MadsRudolph/vinyl-adc/docs/HANDOFF-sim.md

# Handoff — KiCad SPICE testbenches for the vinyl ADC

Paste the block below into a fresh Claude Code session started in
`C:\Users\Mads2\Documents\Projects`.

---

Build the KiCad SPICE testbenches for the discrete delta-sigma vinyl ADC.

**Use the `kicad-schematic` skill**, specifically its fifth gate and
`references/spice-testbenches.md`. `scripts/simfields.py` and
`assets/spice/behavioural.lib` in that skill are the tools; the Class D
amplifier at `Projects/Class D Amplifier/hardware/kicad/sim/` is a complete
worked example of the same job — read `tools/sim_layout.py`, `tools/run_sims.py`
and `README.md` there before starting.

## The project

`Projects/Vinyl ADC/`. The schematic phase is **finished and verified** — do not
redraw it:

- `hardware/kicad/vinyl_adc.kicad_sch`, 121 parts, A2, four bands (power,
  clock/digital, channel L, channel R), generated by
  `hardware/kicad/tools/vinyl_adc_layout.py`
- gates all passing: `sch_score.py` PASS 13/13, ERC clean apart from benign
  `lib_symbol_mismatch`, `tools/check_intent.py` PASS, PDF read twice
- `docs/design-notes.md` is the decision record and the source of every number
  the benches must assert; `docs/bom.md` is the BOM

**Two things about where files go.** There is already a `sim/` directory at the
project root holding the *Python* design tools (`modulator.py`, `components.py`,
`verify.py`, `design_search.py`). That is not this work and must not be touched
or overwritten. Put the KiCad benches in **`hardware/kicad/sim/`**, mirroring the
Class D layout. Also note the project moved into the `Documents\Projects` git
repo and is still untracked there — the stored memory says it lives at
`C:\Users\Mads2\vinyl-adc-project`, which no longer exists; fix that memory.

## What SPICE is for here, and what it is not

The Python model already predicts **68 dB SNR at −8 dBFS** and does it properly,
with long runs and an FFT. **Do not try to reproduce that number in SPICE.**
Reaching 68 dB over a 20 kHz band at 1.536 MHz and OSR 32 needs on the order of
a second of transient at nanosecond steps; it would run for hours and tell you
what `sim/verify.py` already knows.

SPICE's job is the analog reality the Python model idealises:

- op-amp GBW and slew against the TL074's real limits
- the LM311's 200 ns delay and its single-supply threshold
- the charge pump's droop under real load
- where the op-amps actually saturate — which is load-bearing (see below)

Say so on the sheets, so nobody later reads a missing SNR figure as a gap.

## Benches to build

One per block plus a whole-loop sheet, each its own KiCad project. Suggested,
but derive the final list from the schematic's own blocks:

| bench | asserts |
|---|---|
| rails + charge pump | −5 V pump from the 74HC244 with all eight outputs paralleled reaches **≈ −4.1 V at ~32 mA**, ripple **< 1 µV** after 4.7 Ω + 220 µF; pump clocked at **192 kHz** from 4040 Q5 |
| reference | `VREF_P` sits at **2.5 V**; the −2.5 V reference tracks the rail (that is deliberate — it turns rail noise into −98 dB gain modulation instead of additive noise) |
| clock divider | 1.536 MHz in, **4040 Q5 = 192 kHz**, correct division and duty |
| one integrator | gain matches its design coefficient with a real TL074, `a = [0.250, 0.320, 0.610]` normalised to fs |
| quantiser | LM311 on **single +5 V/GND**, summing node biased to +2.5 V, ~200 ns propagation |
| DAC + ELD | 74HC04 swinging 0/5 V into `R_d` with an equal resistor to −2.5 V gives net **±2.5 V**; ELD compensation `k0 = −0.225` |
| **whole loop, one channel** | the payoff sheet — see below |

## The whole-loop bench is the one that matters

Three things to check, in order of importance:

1. **The click test.** A 40 µs transient at 3× full scale, then a normal signal.
   The loop **must recover**. A 1-bit third-order loop that overloads never comes
   back on its own, and on vinyl that is not a corner case. This is the single
   most valuable thing SPICE can tell you here that the schematic cannot.
2. **Where the TL074 actually saturates.** The design has **no clamp parts** — the
   integrator state scales are chosen so the op-amps' own output saturation *is*
   the clamp, at roughly ±2.7 V on ±5 V rails, i.e. 1.3–1.8× Vref. If real
   saturation lands outside that window the rescue mechanism does not work.
   **The rail voltages and the resistor scaling are load-bearing, not arbitrary.**
3. **Integrator swings at −8 dBFS**: 1.43 / 1.47 / 1.45 V. Full scale is
   3.49 Vpk (2.47 Vrms) with the level trimmer at maximum, set by `Rin = 20k5`
   against `Rd1 = 14k7`.

Assert against **those numbers from `design-notes.md`, not against whatever your
models happen to do.** A model and a test that share the same wrong assumption
agree with each other and are both wrong — that has already happened once on the
Class D board, where an inverted comparator model passed its own test.

## Constraints

- **KiCad 10** binaries explicitly: `C:\Program Files\KiCad\10.0\bin\`
- `py -3.13` has `sexpdata`; `C:\Users\Mads2\miniconda3\python.exe` has PySpice
- **Never** run `kicad-cli sch upgrade`
- **Close KiCad before writing any file** it has open
- Every generated `.kicad_pro` needs `wire_width` in its netclasses or the sheet
  renders as invisible hairlines while ERC stays clean
- **No mention of Claude, AI or co-authorship** anywhere in commits or docs

## Done means

- every bench: ERC **0 violations**, `sch_score.py` PASS
- a `run_sims.py` harness that exports each sheet through `kicad-cli` and asserts
  the numbers above, all passing
- the board sheet carries a clickable index of the benches and each bench links
  back (`file:sim/<name>.kicad_sch` — a scheme is required, and point at the
  `.kicad_sch`, not the `.kicad_pro`)
- `design-notes.md` gains a section on what the simulations found, including
  anything that disagrees with the Python model
- committed, and the project's memory updated with the new path
