MadsRudolph/vinyl-adc/media/laser_engraved_lid.png

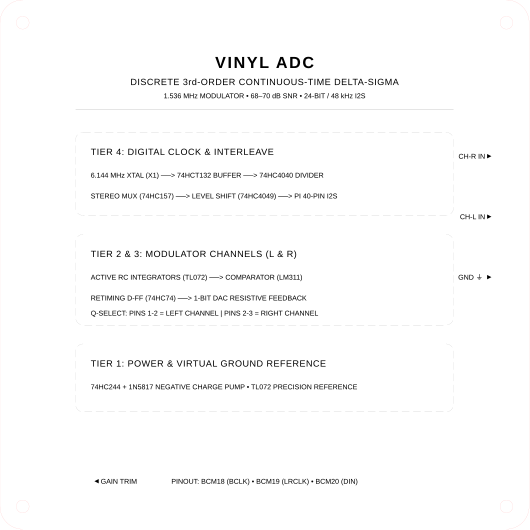
media/laser_engraved_lid.png
