MadsRudolph/vinyl-adc/media/pcb_renders/pcb_channel_top.png

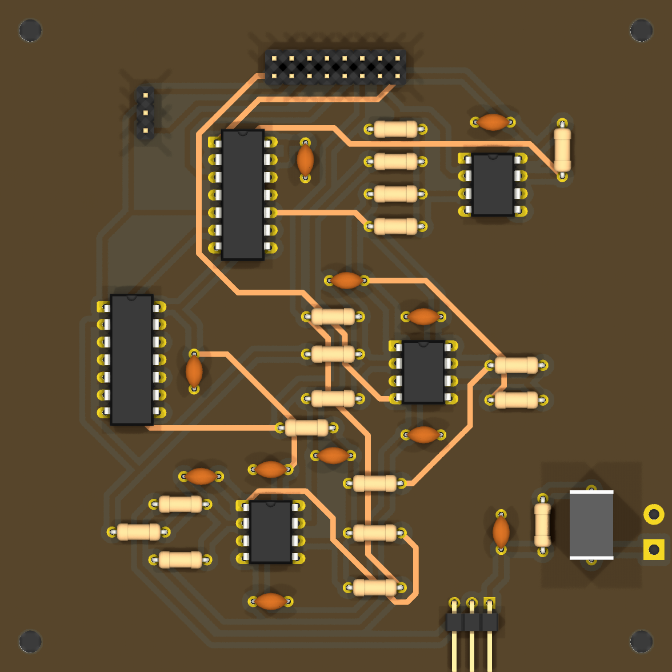
media/pcb_renders/pcb_channel_top.png
