MadsRudolph/vinyl-adc/media/pcb_renders/pcb_digital_top.png

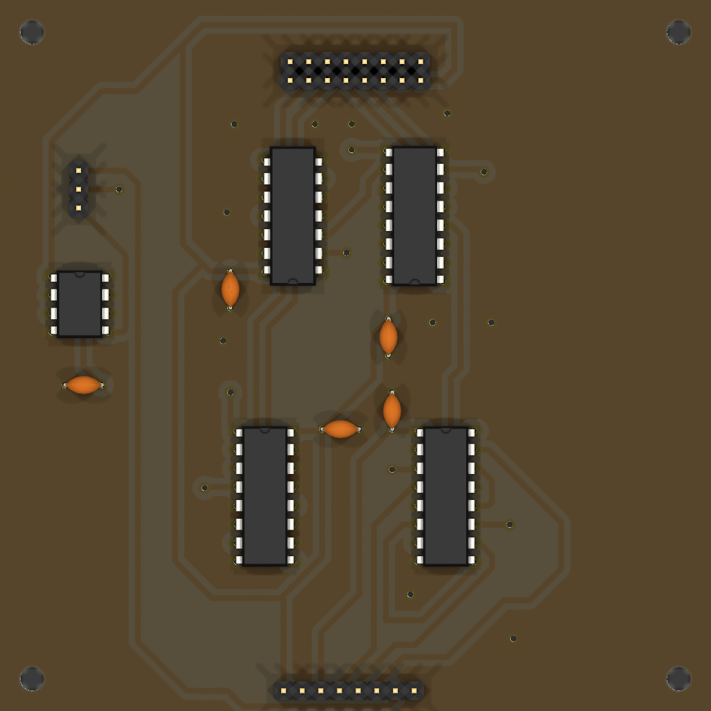
media/pcb_renders/pcb_digital_top.png
