MadsRudolph/vinyl-adc/media/pcb_renders/pcb_power_top.png

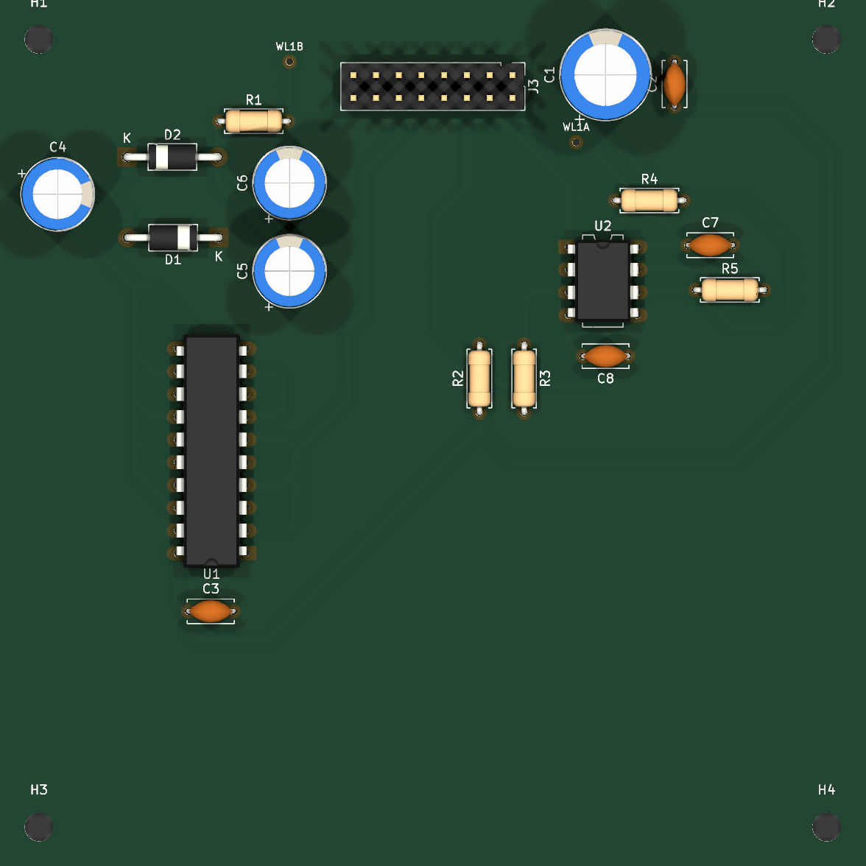
media/pcb_renders/pcb_power_top.png
