MadsRudolph/vinyl-adc/production/vinyl_adc_rev_e/vinyl_adc_rev_e-bottom.png

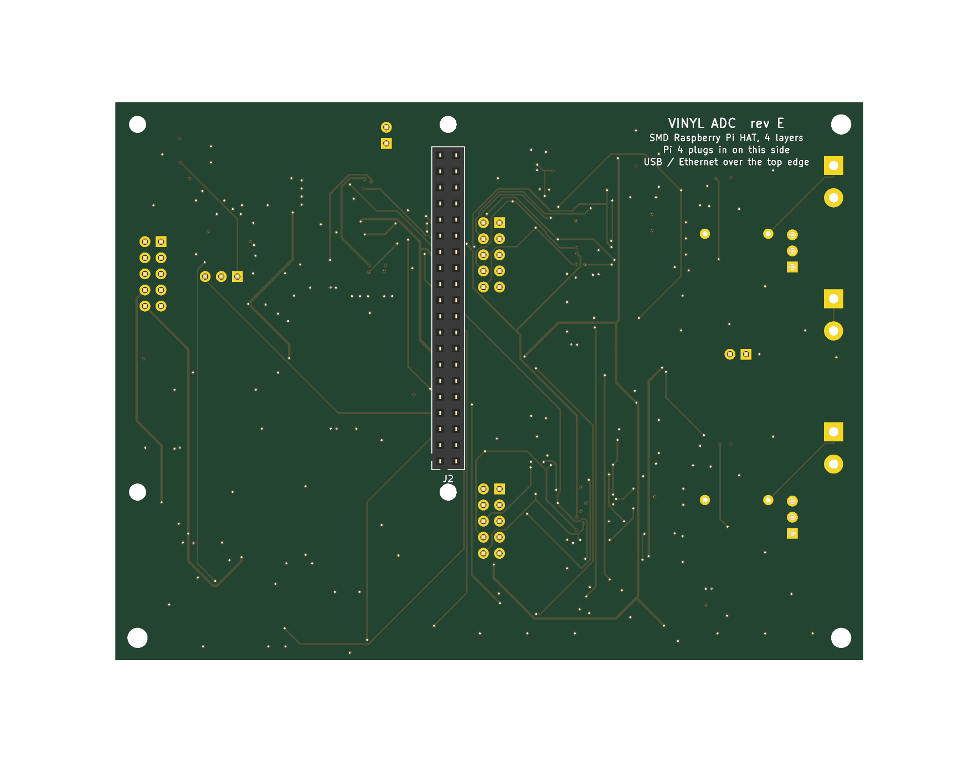
production/vinyl_adc_rev_e/vinyl_adc_rev_e-bottom.png
