MadsRudolph/vinyl-adc/production/vinyl_adc_rev_e/vinyl_adc_rev_e-top.png

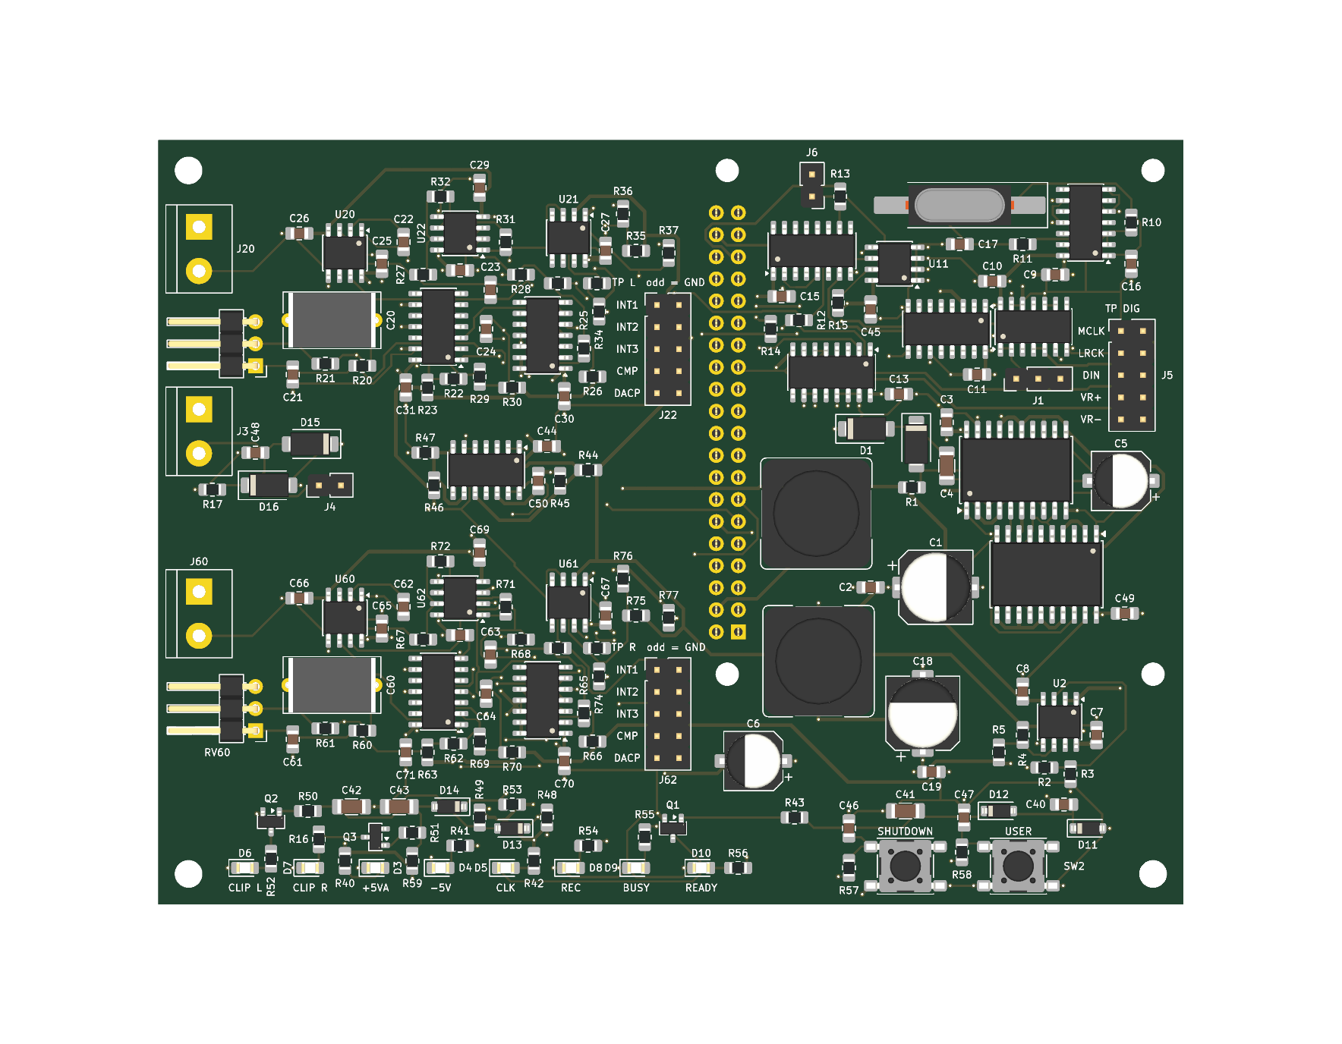
production/vinyl_adc_rev_e/vinyl_adc_rev_e-top.png
