MadsRudolph/vinyl-adc/assembly/sessions/2026-09-06/power-before-clock-fix.png

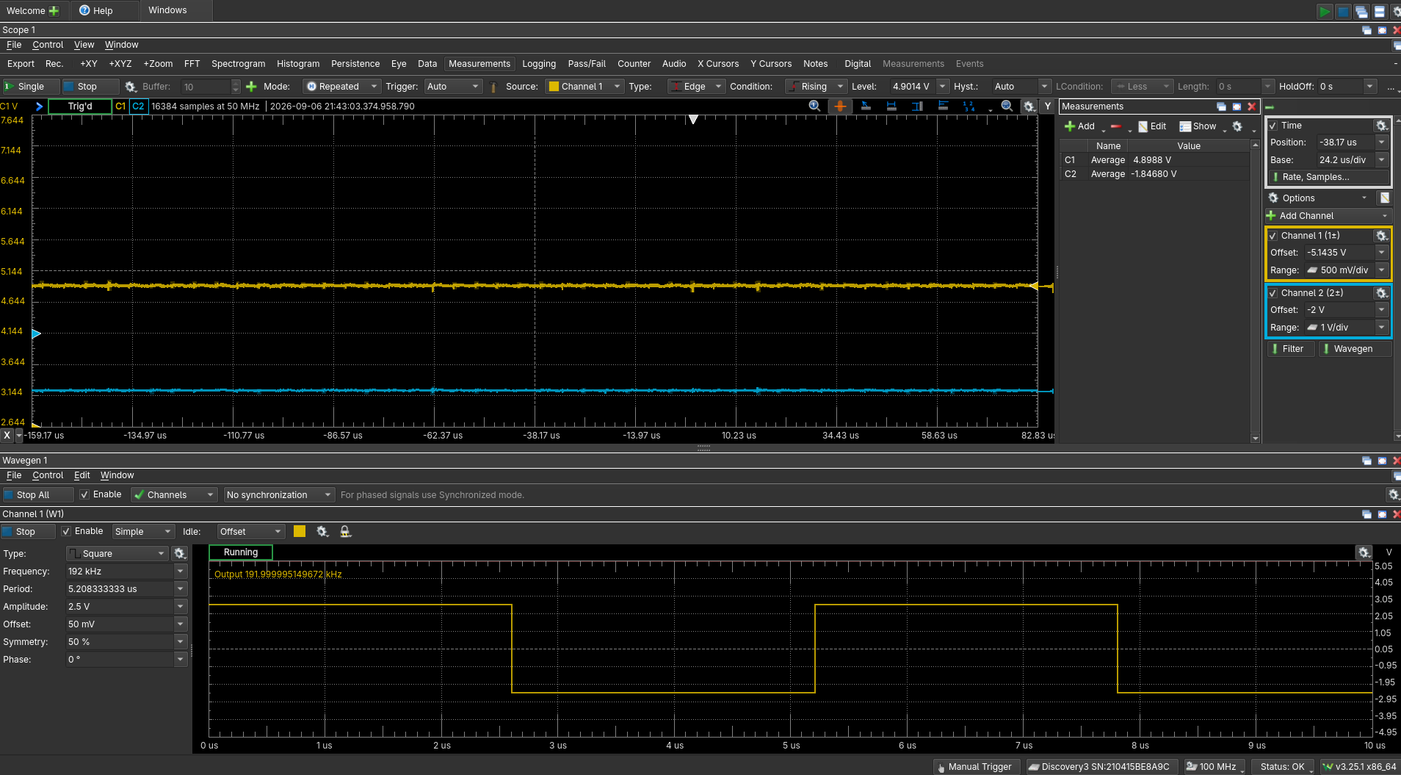
assembly/sessions/2026-09-06/power-before-clock-fix.png
