MadsRudolph/vinyl-adc/production/vinyl_adc_rev_e/vinyl_adc_rev_e-layers.pdf/vinyl_adc_rev_e-Edge_Cuts.pdf

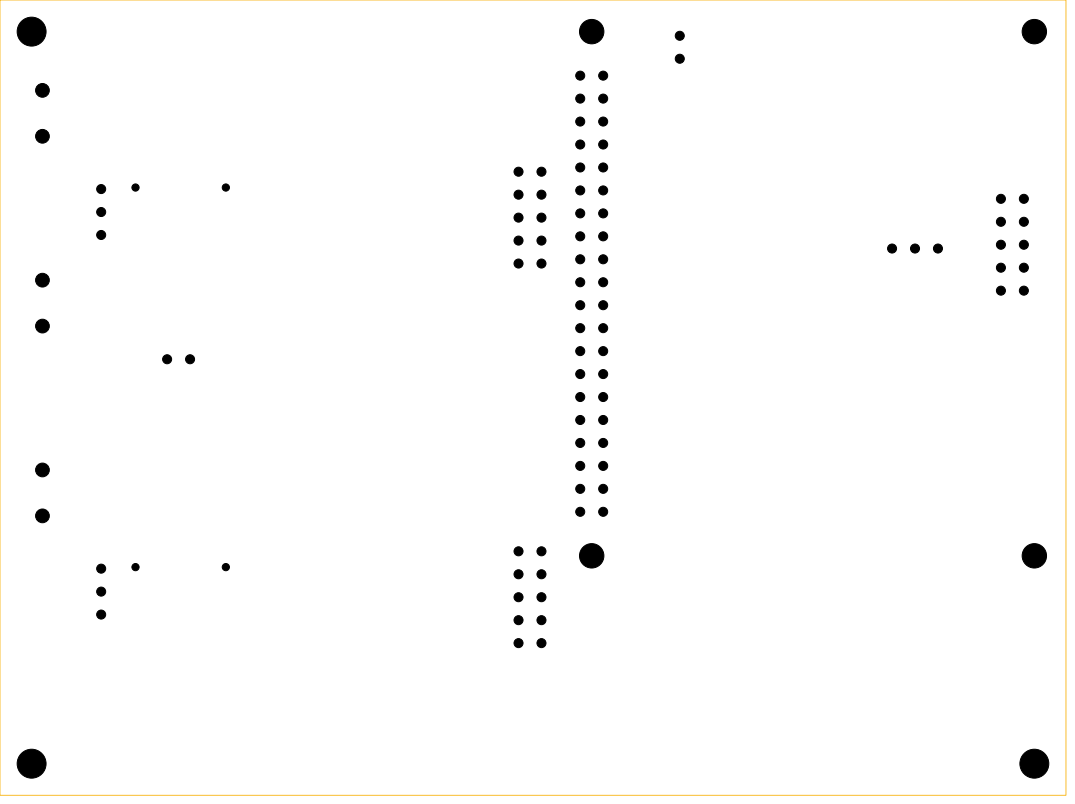
[picture p46: page 1]
