MadsRudolph/vinyl-adc/production/vinyl_adc_rev_e/vinyl_adc_rev_e-layers.pdf/vinyl_adc_rev_e-F_Silkscreen.pdf

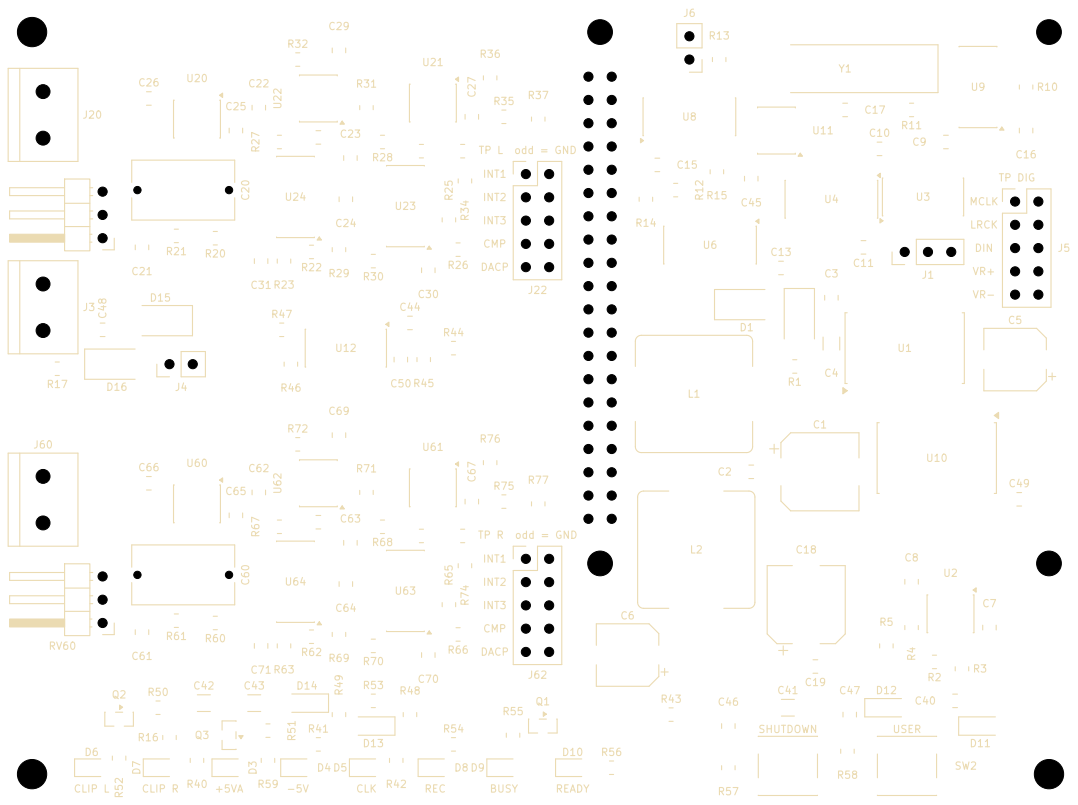
[picture p48: page 1]
