MadsRudolph/vinyl-adc/production/vinyl_adc_rev_e/vinyl_adc_rev_e-layers.pdf/vinyl_adc_rev_e-In1_Cu.pdf

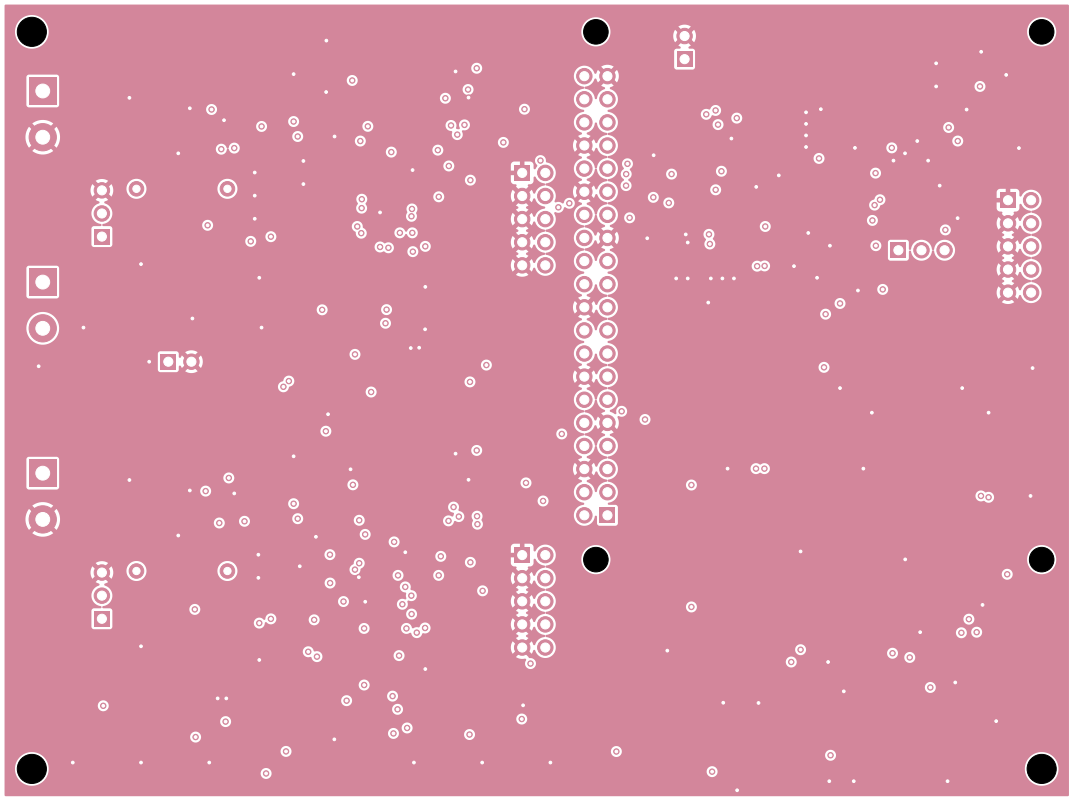
[picture p49: page 1]
