MadsRudolph/vinyl-adc/production/vinyl_adc_rev_e/vinyl_adc_rev_e-layers.pdf/vinyl_adc_rev_e-In2_Cu.pdf

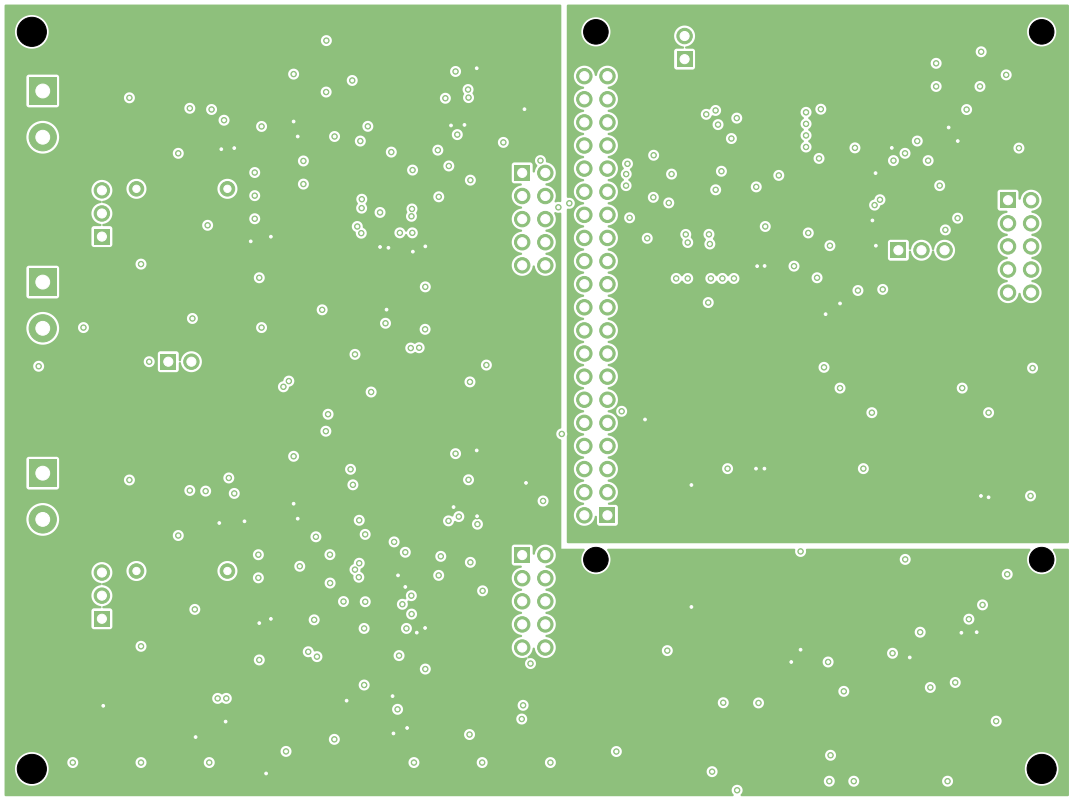
[picture p50: page 1]
