MadsRudolph/vinyl-adc/production/vinyl_adc_rev_d/vinyl_adc_rev_d-layers.pdf/vinyl_adc_rev_d-B_Silkscreen.pdf

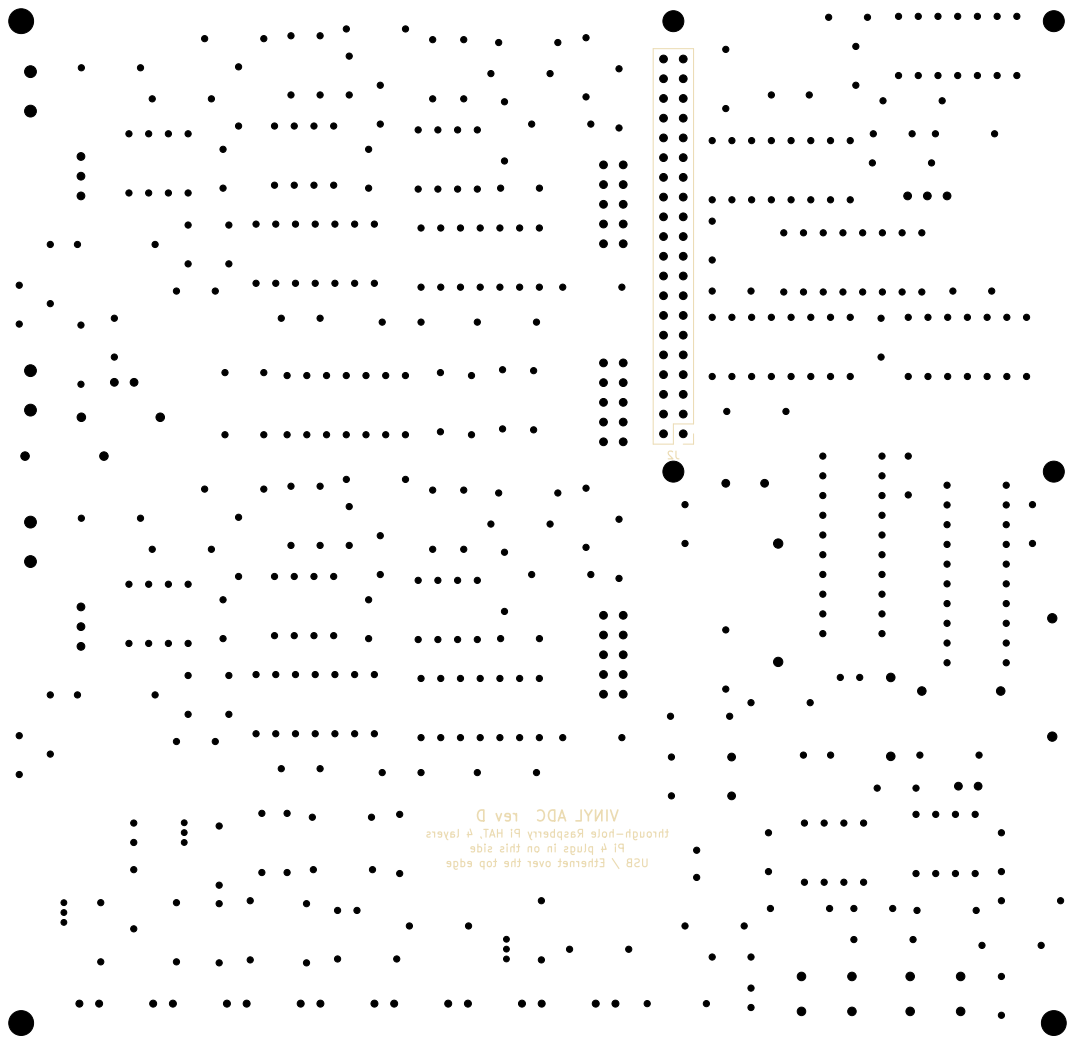
[picture p51: page 1]

layers 4 HAT, Pi Raspberry through-hole side this on in plugs 4 Pi edge top the over Ethernet / USB D rev ADC VINYL
