MadsRudolph/vinyl-adc/production/vinyl_adc_rev_d/vinyl_adc_rev_d-layers.pdf/vinyl_adc_rev_d-F_Silkscreen.pdf

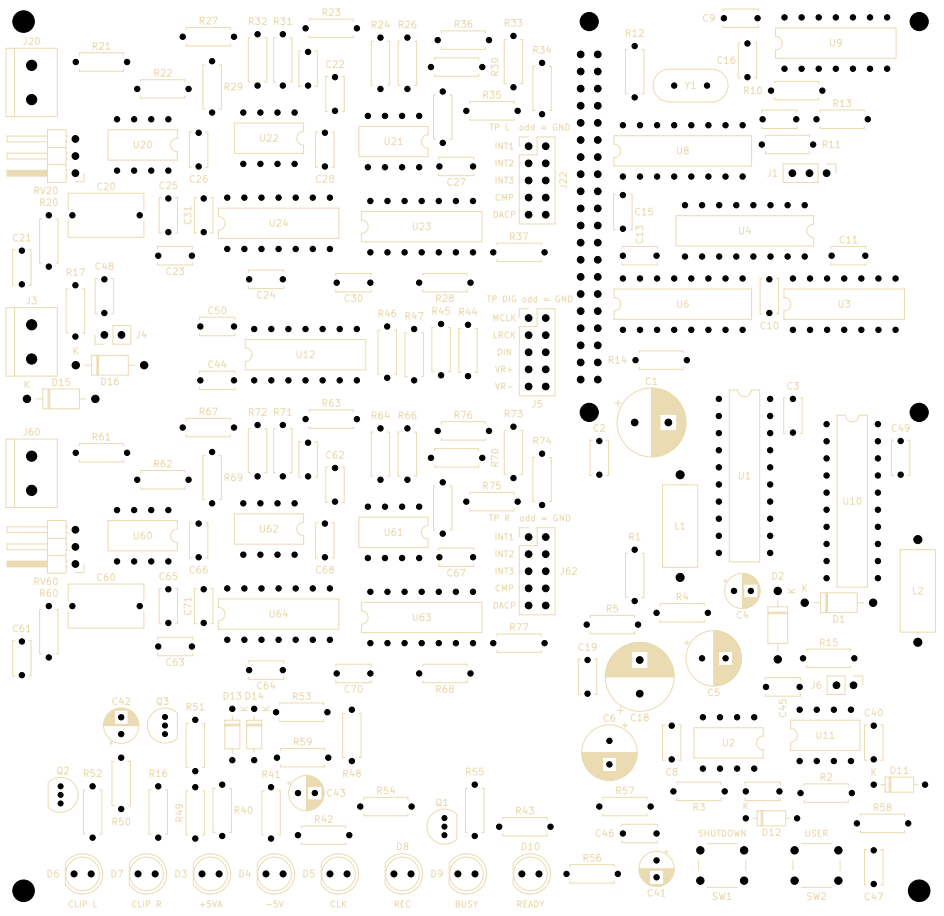
[picture p52: page 1]

TP DIG odd = GND
