MadsRudolph/vinyl-adc/production/vinyl_adc_rev_d/vinyl_adc_rev_d-layers.pdf/vinyl_adc_rev_d-B_Cu.pdf

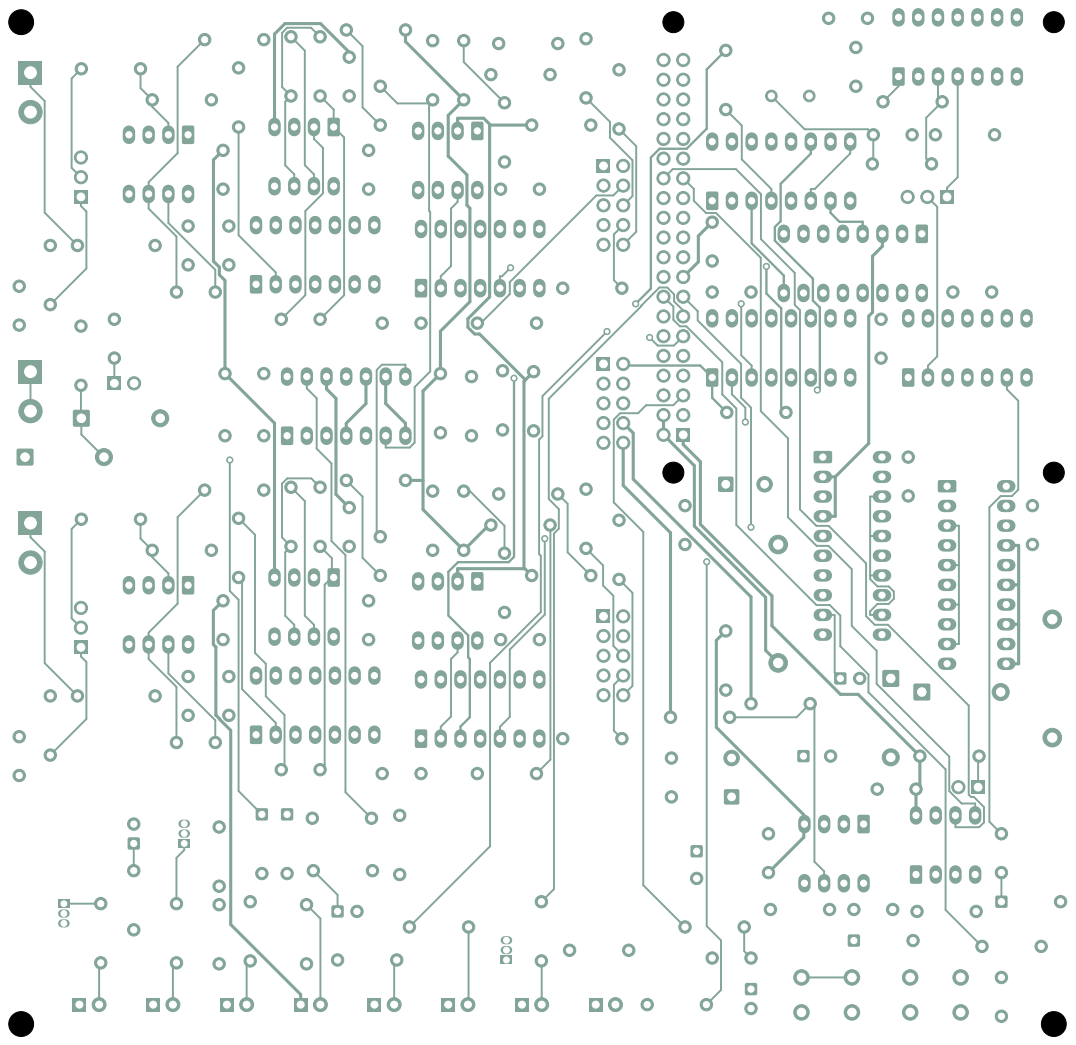
[picture p53: page 1]
