MadsRudolph/vinyl-adc/production/vinyl_adc_rev_d/vinyl_adc_rev_d-layers.pdf/vinyl_adc_rev_d-Edge_Cuts.pdf

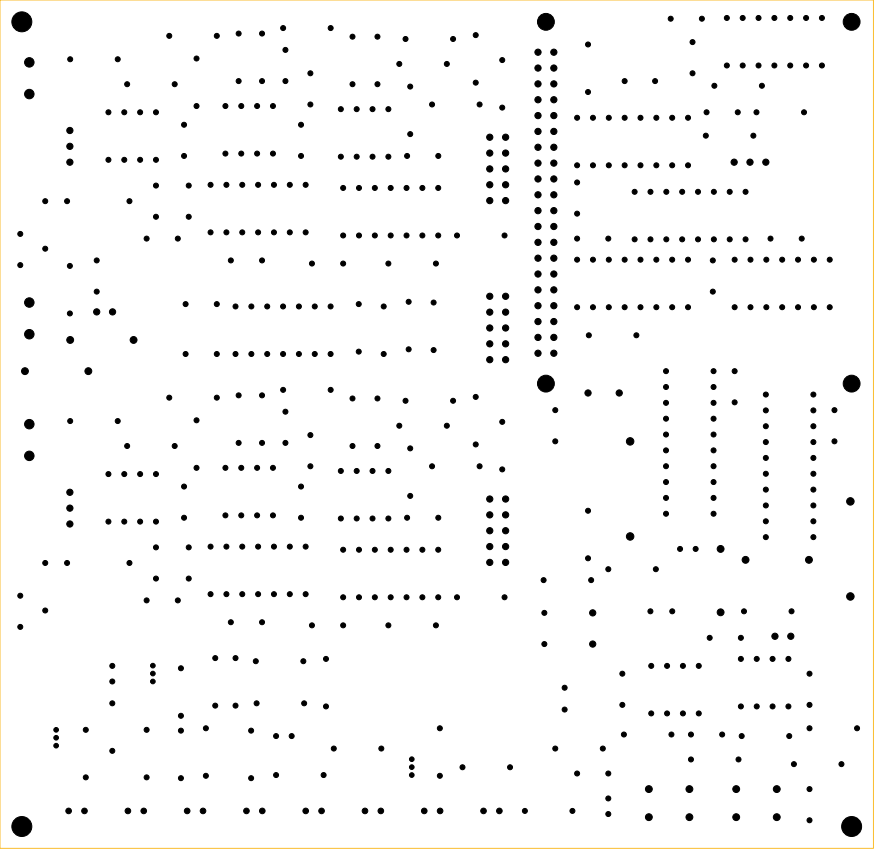
[picture p54: page 1]
