MadsRudolph/vinyl-adc/production/vinyl_adc_rev_d/vinyl_adc_rev_d-layers.pdf/vinyl_adc_rev_d-F_Cu.pdf

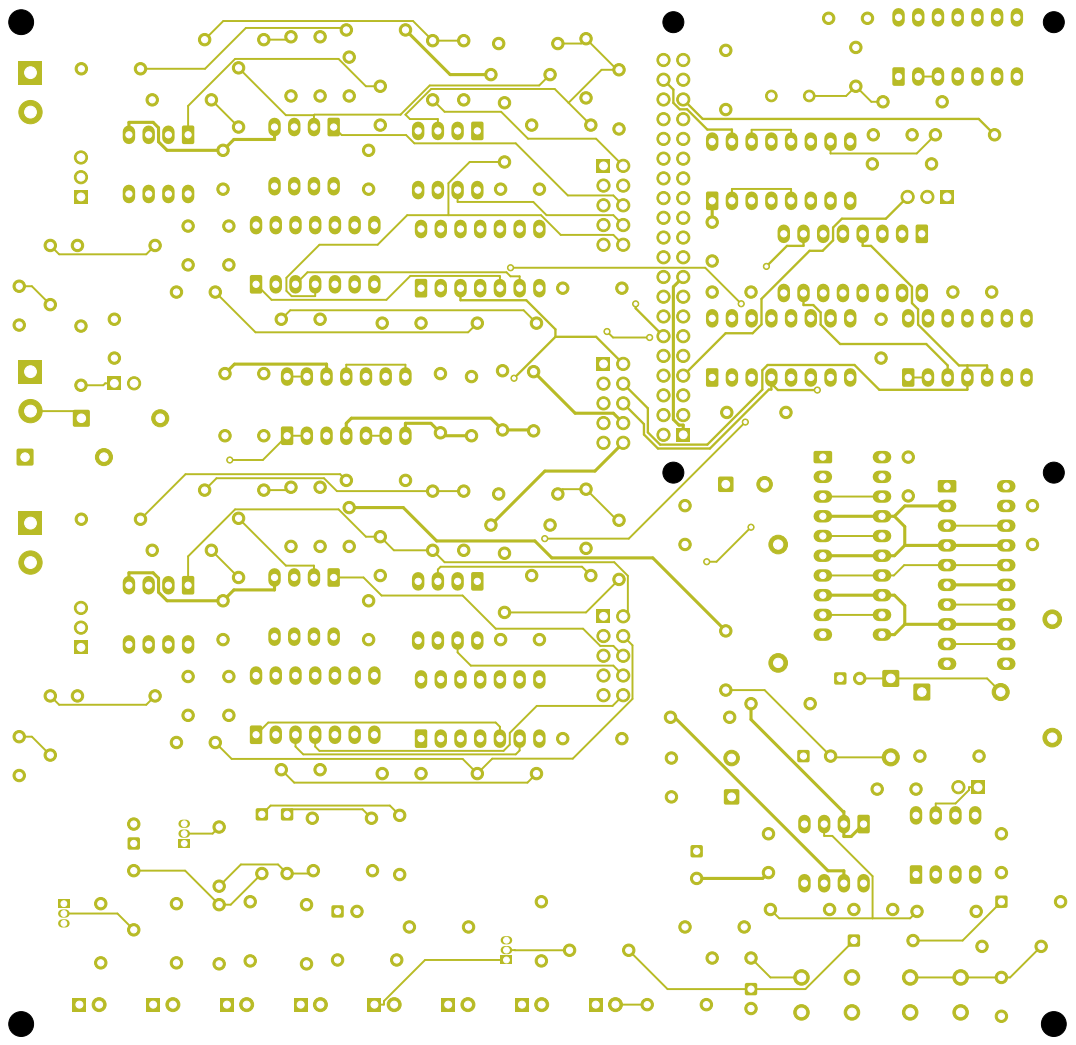
[picture p55: page 1]
