MadsRudolph/vinyl-adc/production/vinyl_adc_rev_c/vinyl_adc_rev_c-layers.pdf/vinyl_adc_rev_c-B_Cu.pdf

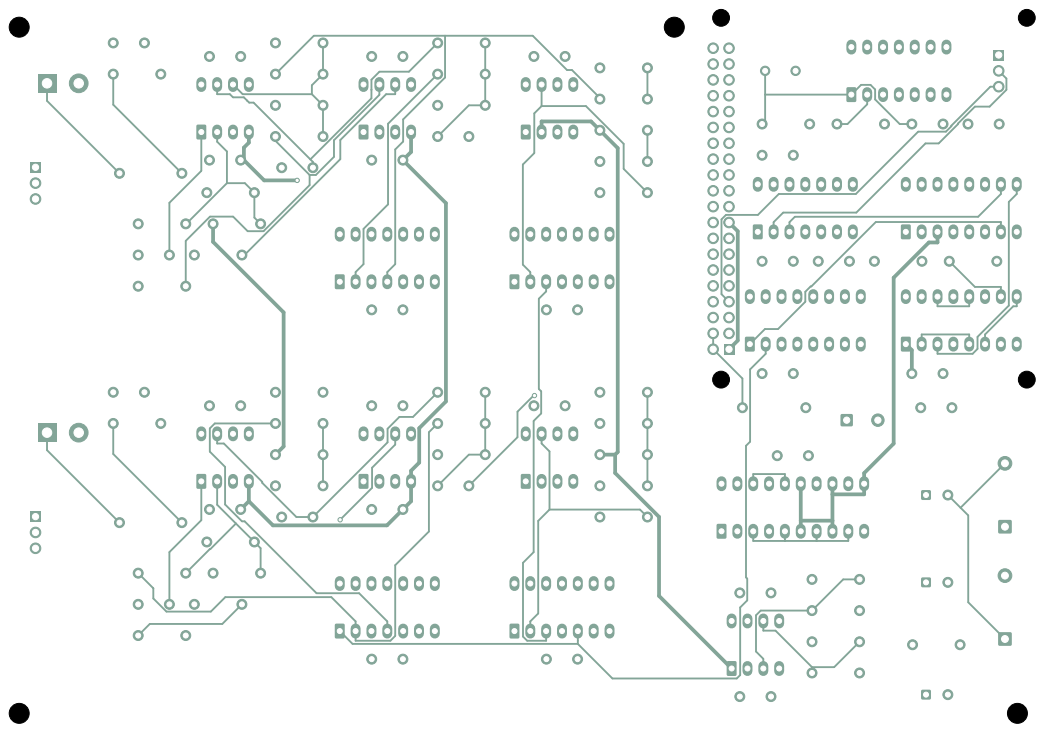
[picture p58: page 1]
