MadsRudolph/vinyl-adc/production/vinyl_adc_rev_c/vinyl_adc_rev_c-layers.pdf/vinyl_adc_rev_c-Edge_Cuts.pdf

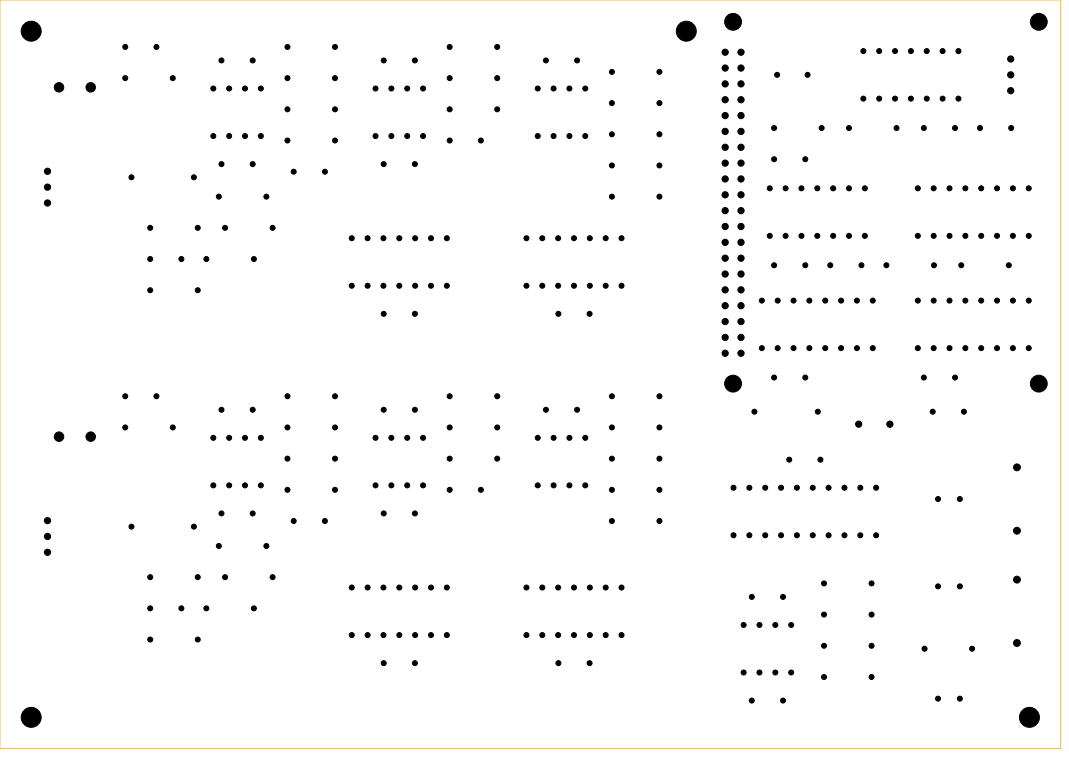
[picture p60: page 1]
