MadsRudolph/vinyl-adc/production/vinyl_adc_rev_c/vinyl_adc_rev_c-layers.pdf/vinyl_adc_rev_c-F_Cu.pdf

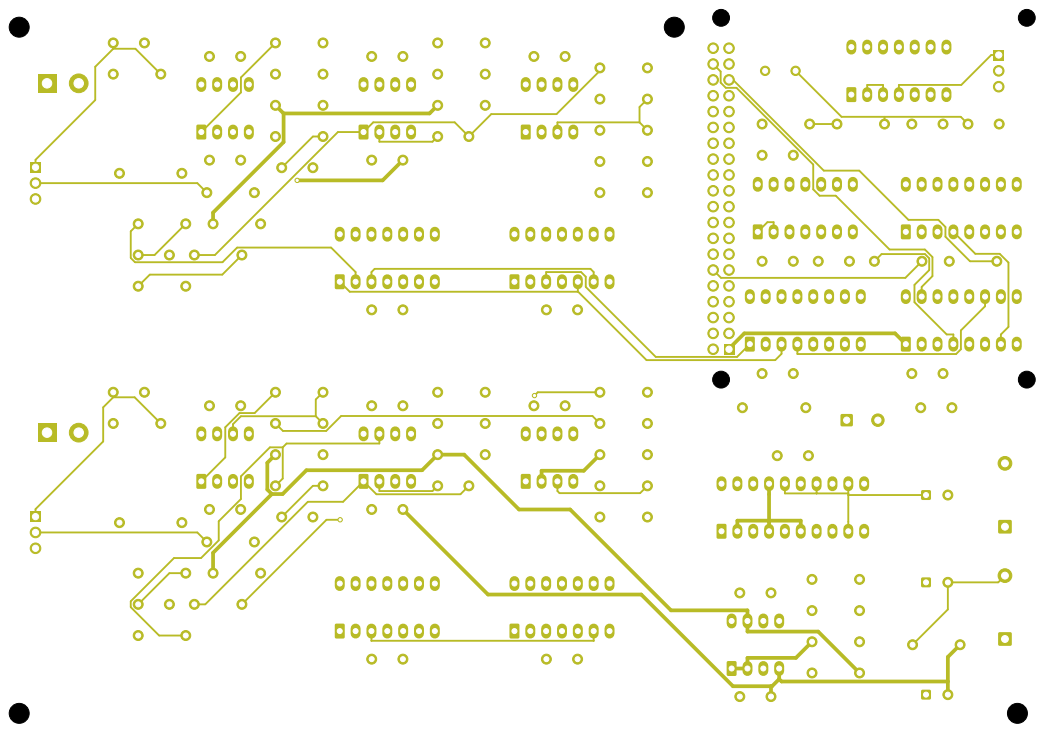
[picture p61: page 1]
