MadsRudolph/vinyl-adc/production/vinyl_adc_rev_c/vinyl_adc_rev_c-layers.pdf/vinyl_adc_rev_c-F_Silkscreen.pdf

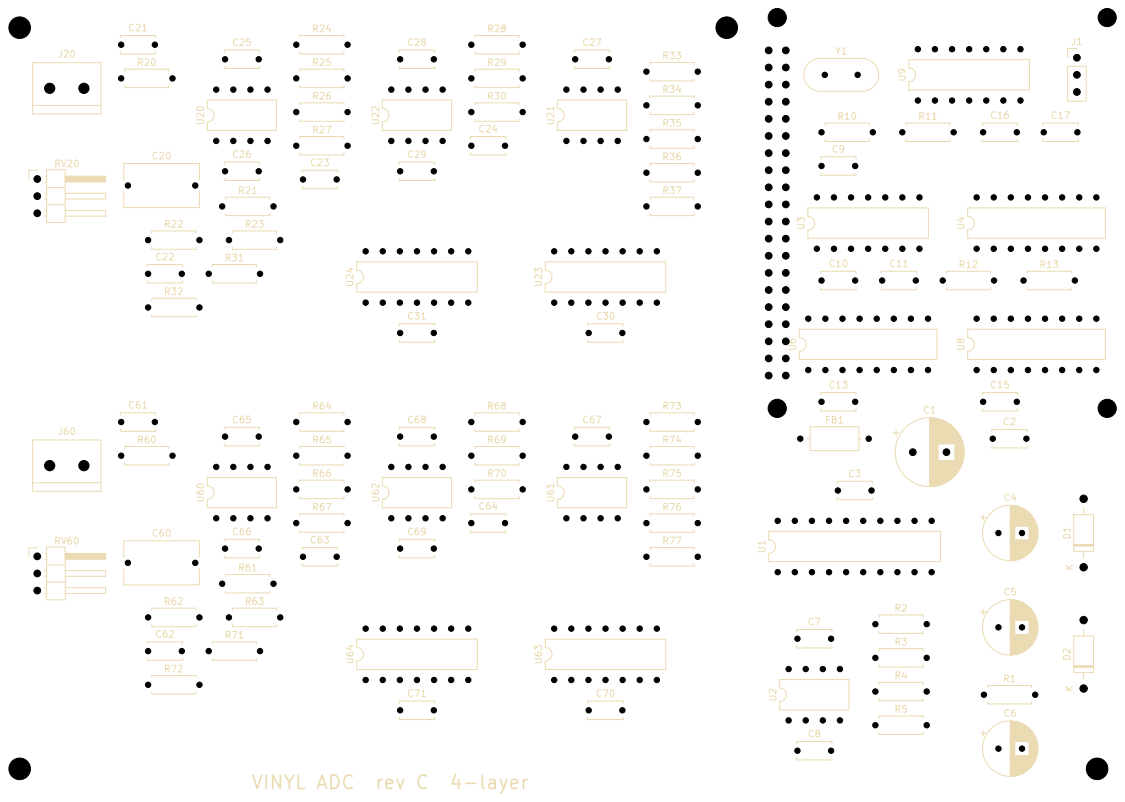
[picture p62: page 1]
