MadsRudolph/vinyl-adc/hardware/kicad/tools/vinyl_adc_layout.py

#!/usr/bin/env python3
"""Layout script for the discrete 3rd-order delta-sigma vinyl ADC.

Run:  py -3.13 vinyl_adc_layout.py  ->  ../vinyl_adc.kicad_sch

Component values come from sim/components.py, which derives them from the
loop coefficients and then re-simulates the snapped E96 values.  Do not
"tidy" a resistor here without re-running that script: the integrator state
scales are chosen so the op-amps saturate at the right level, and that
saturation is the only thing that stops a vinyl click latching the modulator.

Sheet plan (A2, four bands, signal left to right in each):
    A  y~36   power in, charge-pump -5 V, +/-2.5 V reference
    B  y~117  6.144 MHz clock, /4040 divider, quantiser flip-flops,
              interleave mux, DAC gates, level shift, Pi header
    C  y~203  channel L modulator
    D  y~273  channel R modulator
"""

import sys
import os

SKILL = next(p for p in (
    r"C:\Users\Mads2\.claude\skills\kicad-schematic\scripts",
    os.path.expanduser("~/.claude/skills/kicad-schematic/scripts"),
) if os.path.isdir(p))
sys.path.insert(0, SKILL)

from schdraw import Sheet                     # noqa: E402
from simfields import add_hrefs               # noqa: E402

import paths                                   # noqa: E402

G = lambda n: round(n * 1.27, 2)              # noqa: E731

TL07X = "Amplifier_Operational:TL074"
TL072 = "Amplifier_Operational:TL072"
# Bench, 16 September 2026 (design-notes 10b'): the reference inverter U2B
# must sink VREF_N to -2.5 V from a pump rail that sags to -3.8 V under both
# channels, and a TL07x output stops ~2 V above V-.  The LM358 is the one
# stocked drop-in that reaches within a few hundred mV of its rail.
LM358 = "Amplifier_Operational:LM358"
R_LIB, C_LIB = "Device:R", "Device:C"
CP_LIB = "Device:C_Polarized"

COL = G(8)           # 10.16  pitch of summing-input rows
FB = G(9)            # 11.43  op-amp centreline -> feedback row
STUB = G(4)          # 5.08

TITLE = "Discrete 3rd-order delta-sigma vinyl ADC  -  stereo, 48 kHz"


def new_sheet(title=TITLE, project="vinyl_adc", paper="A2"):
    return Sheet(paper=paper, title=title, project=project)


# ---------------------------------------------------------------- helpers ---

def ic_supply(sh, part, vcc, gnd, cref, x_cap, rail="+5V"):
    """VCC up to a rail symbol, GND down to a GND symbol, 100n across."""
    vp, vn = part.pin(vcc), part.pin(gnd)
    ytop, ybot = vp.y - STUB, vn.y + STUB
    sh.seg(vp, (vp.x, ytop))
    sh.seg((vp.x, ytop), (x_cap, ytop))
    sh.rail((x_cap, ytop), net=rail, rise=STUB)
    sh.seg(vn, (vn.x, ybot))
    sh.seg((vn.x, ybot), (x_cap, ybot))
    c = sh.place(C_LIB, cref, at=(x_cap, round((ytop + ybot) / 2 / 1.27) * 1.27),
                 rot=0, value="100n")
    sh.seg((x_cap, ytop), c.pin(1))
    sh.seg(c.pin(2), (x_cap, ybot))
    sh.gnd((x_cap, ybot))


def opamp_supply(sh, uref, at, ca_ref, cb_ref, unit=3, lib=None,
                 value="TL072", rail="+5V"):
    """A dual-supply op-amp package's power unit, with its two 100n.

    The caps sit in series across the rails with the midpoint grounded, so
    each rail gets a 100n to ground and the pair also decouples rail to rail,
    which is the loop the op-amp's own supply current actually takes.

    `rail` is the positive supply: +5V on every milled board, +5VA -- the
    analog island behind its own choke -- on rev D.
    """
    sup = sh.place(lib or TL072, uref, at=at, unit=unit, value=value)
    vp, vn = sup.pin("V+"), sup.pin("V-")
    sh.seg(vp, (vp.x, vp.y - STUB))
    sh.rail((vp.x, vp.y - STUB), net=rail, rise=STUB)
    sh.seg(vn, (vn.x, vn.y + STUB))
    sh.rail((vn.x, vn.y + STUB), net="-5V", rise=-STUB)
    cx = vp.x + G(10)
    ca = sh.place(C_LIB, ca_ref, at=(cx, vp.y - STUB + G(3)), rot=0,
                  value="100n")
    cb = sh.place(C_LIB, cb_ref, at=(cx, vn.y + STUB - G(3)), rot=0,
                  value="100n")
    sh.seg((vp.x, vp.y - STUB), (cx, vp.y - STUB))
    sh.seg((cx, vp.y - STUB), ca.pin(1))
    sh.seg(ca.pin(2), cb.pin(1))
    sh.seg(cb.pin(2), (cx, vn.y + STUB))
    sh.seg((vn.x, vn.y + STUB), (cx, vn.y + STUB))
    gy = round((ca.pin(2).y + cb.pin(1).y) / 2 / 1.27) * 1.27
    sh.seg((cx, gy), (cx + G(6), gy))
    sh.power("power:GND", (cx + G(6), gy), rot=270)
    return sup


def note_block(sh, at, text, size=1.27):
    """Multi-line annotation, one note_block() per line.

    schdraw writes note text into the s-expression verbatim, so a string with
    an embedded newline produces a raw newline inside a quoted token and KiCad
    10 refuses to load the whole file -- while sch_score and the in-process
    checks all still pass.  Splitting the lines here side-steps it.
    """
    x, y = at
    step = 1.27 * max(2, round(size * 1.6 / 1.27))
    for i, line in enumerate(str(text).splitlines() or [""]):
        sh.note((x, y + i * step), line, size=size)


def gate_pins(part, at_x):
    """(left pins, right pins) of a gate unit, top to bottom.

    Unit pin ORDER is not consistent across a package -- 74HC04 unit 4 lists
    its output first -- so pick inputs and outputs by which side of the symbol
    they sit on rather than by index.
    """
    left = sorted([q for q in part.pins if q.x < at_x], key=lambda q: q.y)
    right = sorted([q for q in part.pins if q.x > at_x], key=lambda q: q.y)
    return left, right


def tie_low(sh, *pins):
    """Unused CMOS inputs must not float: one shared bus, one GND symbol.

    Giving each pin its own downward GND drop looks tidier and is WRONG: on a
    2.54 mm pin pitch a 5.08 mm drop ends exactly on the next pin's stub, so
    KiCad puts a junction there and the two pins short.  That is how the whole
    74HC157 ended up on one net.""" 
    ps = sorted(pins, key=lambda q: q.y)
    x = min(q.x for q in ps) - STUB
    for q in ps:
        sh.seg(q, (x, q.y))
    if len(ps) > 1:
        sh.seg((x, ps[0].y), (x, ps[-1].y))
    # drop=0: the symbol hangs straight off the end of the bus.  A 5.08 drop
    # here is what shorted MCLK to ground -- it landed exactly on the mux's
    # select-pin stub one row below.
    sh.gnd((x, ps[-1].y), drop=0)


def summing_stage(sh, x, y0, rows, uref, unit, fb_kind, fb_ref, fb_val,
                      opamp=TL07X, title=None, title_dy=G(-20)):
    """One inverting stage: N summing inputs -> virtual earth -> op-amp.

    `rows` is a list of (global_label_or_None, refdes, value); a None label
    means that row is the block's signal input port, wired by the caller.
    `fb_kind` is "C" for an integrator or "R" for a plain inverter.

    Returns dict with in/out ports and the resistor parts.
    """
    n = len(rows)
    y_s = y0 + (n - 1) * COL / 2.0
    y_s = round(y_s / 1.27) * 1.27
    y_bot = y0 + (n - 1) * COL
    y_fb = max(y_s + FB, y_bot + G(8))
    bus_x = x + G(21)                      # 26.67

    u = sh.place(opamp, uref, at=(x + G(38), y_s - G(2)), unit=unit,
                 value=opamp.split(":")[1])
    plus, minus, out = u.pin("+"), u.pin("-"), u.pin("out")

    parts = {}
    for i, (lbl, rref, rval) in enumerate(rows):
        ry = y0 + i * COL
        r = sh.place(R_LIB, rref, at=(x + G(12), ry), rot=90, value=rval)
        sh.seg((x, ry), r.pin(1))
        sh.seg(r.pin(2), (bus_x, ry))
        if lbl:
            sh.label((x, ry), lbl, kind="global")
        parts[rref] = r

    sh.seg((bus_x, y0), (bus_x, y_bot))                    # the summing bus
    sh.seg((bus_x, y_s), minus)

    lib = C_LIB if fb_kind == "C" else R_LIB
    fb = sh.place(lib, fb_ref, at=(x + G(38), y_fb), rot=90, value=fb_val)
    sh.seg((x + G(29), y_s), (x + G(29), y_fb))            # tap down
    sh.seg((x + G(29), y_fb), fb.pin(1))
    sh.seg(fb.pin(2), (x + G(46), y_fb))
    sh.seg((x + G(46), y_fb), (x + G(46), y_s - G(2)))
    sh.seg(out, (x + G(52), y_s - G(2)))                   # output run

    # `+` to ground: leaves left and descends, crossing the bus->`-` lead
    sh.seg(plus, (x + G(25), y_s - G(4)))
    sh.seg((x + G(25), y_s - G(4)), (x + G(25), y_fb + G(8)))
    sh.gnd((x + G(25), y_fb + G(8)))

    if title:
        note_block(sh, (x, y0 + title_dy), title, size=2.0)

    return {"in": (x, y0), "out": (x + G(52), y_s - G(2)),
            "y_out": y_s - G(2), "parts": parts, "u": u, "y_fb": y_fb}


def elbow(sh, a, b, xmid):
    """Route a -> b as horizontal, vertical, horizontal through xmid."""
    ax, ay = a
    bx, by = b
    sh.seg((ax, ay), (xmid, ay))
    sh.seg((xmid, ay), (xmid, by))
    sh.seg((xmid, by), (bx, by))


def dogleg(sh, a, b, ymid):
    """Route a -> b as vertical, horizontal, vertical through ymid.

    The other way round from elbow(), for a run that has to leave the block
    the short way and travel the long way in a clear channel.
    """
    ax, ay = a
    bx, by = b
    sh.seg((ax, ay), (ax, ymid))
    sh.seg((ax, ymid), (bx, ymid))
    sh.seg((bx, ymid), (bx, by))


# The SPICE testbenches in sim/, as a clickable index.
#
# Hyperlinks, not hierarchical sheets.  Attaching a bench as a sheet of this
# project was measured on another board and it is wrong three ways: the
# bench's supply welds onto the board's real rail because power symbols are
# global across a hierarchy, its sources land in the board netlist ready for
# Update PCB from Schematic to put them on copper, and any refdes it shares
# with the board silently merges with it.  A hierarchy is one electrical
# design; these are eight separate ones.
#
# The href needs a scheme.  A bare relative path, or a bare ${KIPRJMOD}/...,
# is rejected when the file loads -- so the schematic reads as CORRUPT rather
# than as a broken link.  "file:sim/x.kicad_sch" carries a scheme and stays
# relative, so it survives the repository being cloned anywhere.  It points
# at the .kicad_sch and not the .kicad_pro because the OS opens a project
# file with the project manager, one click short of the drawing.
SIM_LINKS = [
    ("SPICE TESTBENCHES  (sim/, one project each -- click to open)", None),
    ("A  rails and the -5 V charge pump", "sim_a_pump"),
    ("B  the +/-2.5 V ratiometric reference", "sim_b_reference"),
    ("C  clock buffer and 74HC4040 divider", "sim_c_clock"),
    ("D  integrator 1 with a real TL074", "sim_d_integrator"),
    ("E  LM311 quantiser on a single supply", "sim_e_quantiser"),
    ("F  the 1-bit DAC and its offset leg", "sim_f_dac"),
    ("G  retiming, interleave and the 3.3 V level shift", "sim_g_interface"),
    ("H  one complete channel, with the click test", "sim_h_loop"),
]


def sim_index(sh, x, y):
    """Draw the testbench index and return {text: href} for add_hrefs()."""
    links = {}
    for i, (text, name) in enumerate(SIM_LINKS):
        sh.note((x, y + i * G(4)), text, size=1.6 if name else 1.8)
        if name:
            links[text] = f"file:sim/{name}.kicad_sch"
    return links


# =============================================================== BAND A: POWER

def charge_pump(sh, px, y, second=None):
    """The -5 V rail: a 74HC244 with all eight buffers paralleled, two
    Schottkys and an RC post-filter.

    `second` = (refdes, cap refdes) adds a SECOND 74HC244 below the first
    with its eight outputs on the same node -- rev D.  The pump's 16 ohm
    output resistance is the drivers' own on-resistance (design-notes 10b),
    so sixteen buffers halve it and lift the rail from about -3.8 V to
    about -4.4 V under both channels, which is the TL072 common-mode margin
    that section flagged as the one thing worth acting on.

    There is no charge-pump IC in the DTU shop, so the driver is eight bus
    buffers in parallel -- about 32 mA, which is the whole analog budget and
    the reason the comparators run single-supply (docs/design-notes.md 6).

    D1 returns the pump node to ground on the driver's HIGH half, so its
    ANODE faces the pump node; D2 hands the negative excursion to the
    reservoir on the LOW half, so its CATHODE faces the pump node.  Reverse
    either and the circuit is a voltage doubler making about +4.5 V, which is
    what sim_a_pump exists to catch -- it was drawn that way, and every other
    gate in this toolkit passed it.
    """
    u1 = sh.place("74xx:74HC244", "U1", at=(px, y + G(12)), value="74HC244")
    ins = [u1.pin(n) for n in (2, 4, 6, 8, 17, 15, 13, 11)]
    outs = [u1.pin(n) for n in (18, 16, 14, 12, 3, 5, 7, 9)]
    xin = ins[0].x - G(6)
    for p in ins:
        sh.seg(p, (xin, p.y))
    sh.seg((xin, ins[0].y), (xin, ins[-1].y))
    sh.seg((xin, ins[0].y), (xin - G(6), ins[0].y))
    sh.label((xin - G(6), ins[0].y), "PUMP", kind="global")
    xout = outs[0].x + G(6)
    for p in outs:
        sh.seg(p, (xout, p.y))
    sh.seg((xout, outs[0].y), (xout, outs[-1].y))
    tie_low(sh, u1.pin(1), u1.pin(19))                         # both /OE low
    ic_supply(sh, u1, 20, 10, "C3", px + G(24))
    if second:
        # same drawing again, G(48) lower: the pin rows share the two
        # vertical buses, so the second package simply extends them.  The
        # symbol is G(16) each side of its origin, so at G(56) the second
        # package's +5V rail symbol landed exactly on the first one's GND
        # symbol and the two rails merged -- ERC's pin_to_pin caught it.
        uref, cref = second
        u2_ = sh.place("74xx:74HC244", uref, at=(px, y + G(60)),
                       value="74HC244")
        ins2 = [u2_.pin(n) for n in (2, 4, 6, 8, 17, 15, 13, 11)]
        outs2 = [u2_.pin(n) for n in (18, 16, 14, 12, 3, 5, 7, 9)]
        for p in ins2:
            sh.seg(p, (xin, p.y))
        sh.seg((xin, ins[-1].y), (xin, ins2[-1].y))
        for p in outs2:
            sh.seg(p, (xout, p.y))
        sh.seg((xout, outs[-1].y), (xout, outs2[-1].y))
        tie_low(sh, u2_.pin(1), u2_.pin(19))
        ic_supply(sh, u2_, 20, 10, cref, px + G(24))
        note_block(sh, (px - G(14), y - G(6)),
                "2 x 8 buffers paralleled: half the 16 ohm output\n"
                "resistance of one package, ~0.6 V more rail (10b)",
                size=1.27)
    else:
        note_block(sh, (px - G(14), y - G(6)),
                "8 buffers paralleled ~= 32 mA;\nno charge-pump IC in the shop",
                size=1.27)

    # pump capacitor, rectifier, reservoir
    cy = outs[0].y
    c4 = sh.place(CP_LIB, "C4", at=(xout + G(8), cy), rot=90, value="10u")
    sh.seg((xout, cy), c4.pin(1))
    nx = c4.pin(2).x + G(6)
    sh.seg(c4.pin(2), (nx, cy))
    # D1 returns the pump node to ground on the driver's HIGH half, so its
    # ANODE faces the pump node; D2 hands the negative excursion to the
    # reservoir on the LOW half, so its CATHODE faces the pump node.
    #
    # Device:D_Schottky numbers pin 1 = K and pin 2 = A -- cathode first, which
    # is the opposite of the reading that seems natural -- and at rot=90 pin 1
    # lands at the BOTTOM.  Both diodes were drawn that way round, which makes
    # this a positive voltage doubler: sim/sim_a_pump measured +3.4 V on the
    # net called -5V.  Nothing else caught it.  sch_score, ERC, the netlist
    # read-back and check_intent.py all passed on the reversed version,
    # because a diode connected the wrong way round is still connected.
    d1 = sh.place("Device:D_Schottky", "D1", at=(nx, cy - G(8)), rot=270,
                  value="1N5817")
    sh.seg((nx, cy), d1.pin(2))
    sh.seg(d1.pin(1), (nx, cy - G(14)))
    sh.gnd((nx, cy - G(14)), drop=0)
    d2 = sh.place("Device:D_Schottky", "D2", at=(nx, cy + G(8)), rot=270,
                  value="1N5817")
    sh.seg((nx, cy), d2.pin(1))
    sh.seg(d2.pin(2), (nx, cy + G(14)))
    ry = cy + G(14)
    c5 = sh.place(CP_LIB, "C5", at=(nx + G(10), ry + G(6)), rot=180,
                  value="220u")
    sh.seg((nx, ry), (nx + G(10), ry))
    sh.seg((nx + G(10), ry), c5.pin(2))
    sh.seg(c5.pin(1), (nx + G(10), ry + G(12)))
    sh.gnd((nx + G(10), ry + G(12)))
    r1 = sh.place(R_LIB, "R1", at=(nx + G(18), ry), rot=90, value="4R75")
    sh.seg((nx + G(10), ry), r1.pin(1))
    c6 = sh.place(CP_LIB, "C6", at=(nx + G(26), ry + G(6)), rot=180,
                  value="220u")
    sh.seg(r1.pin(2), (nx + G(26), ry))
    sh.seg((nx + G(26), ry), c6.pin(2))
    sh.seg(c6.pin(1), (nx + G(26), ry + G(12)))
    sh.gnd((nx + G(26), ry + G(12)))
    sh.seg((nx + G(26), ry), (nx + G(30), ry))
    sh.rail((nx + G(30), ry), net="-5V", rise=-STUB)
    note_block(sh, (nx - G(4), ry + G(19)),
            "192 kHz pump drive = 4x the 48 kHz output rate,\n"
            "so residual ripple lands on a CIC decimator null.", size=1.27)
    return {"node": (nx, cy), "out": (nx + G(30), ry), "u": u1}


def reference(sh, rx, y, opamp=TL072, refs=("U2", "U2"), supply=True,
              rail="+5V"):
    """The +/-2.5 V DAC reference, ratiometric off the same +5 V rail.

    Deliberately NOT filtered: because the divider tracks the rail the gate
    runs on, rail noise appears as a common-mode gain modulation at -98 dB
    instead of as additive noise, and filtering the reference would break
    that cancellation (docs/design-notes.md 6).

    `refs`/`supply` exist for the testbench: KiCad's SPICE exporter has no
    notion of symbol units, so a bench needs one refdes and one single-unit
    symbol per section, and it wires the rails itself instead of hanging a
    package supply unit off the pair.

    Returns the two op-amp sections.
    """
    note_block(sh, (rx - G(8), y - G(16)),
            "REFERENCE  (+/-2.5V, ratiometric -- tracks +5V so rail noise "
            "cancels as gain, not additive noise)", size=2.0)
    r2 = sh.place(R_LIB, "R2", at=(rx, y + G(2)), rot=0, value="10k0")
    r3 = sh.place(R_LIB, "R3", at=(rx, y + G(12)), rot=0, value="10k0")
    sh.seg(r2.pin(1), (rx, y - G(2)))
    sh.rail((rx, y - G(2)), net=rail, rise=STUB)
    sh.seg(r2.pin(2), r3.pin(1))
    sh.seg(r3.pin(2), (rx, y + G(18)))
    sh.gnd((rx, y + G(18)))
    mid = r2.pin(2).y + (r3.pin(1).y - r2.pin(2).y) / 2
    mid = round(mid / 1.27) * 1.27

    u2a = sh.place(opamp, refs[0], at=(rx + G(16), mid + G(2)),
                   unit=1, value=opamp.split(":")[1])
    sh.seg((rx, mid), (u2a.pin("+").x, mid))
    sh.seg(u2a.pin("out"), (u2a.pin("out").x + G(4), mid + G(2)))
    fbx = u2a.pin("out").x + G(4)
    sh.seg((fbx, mid + G(2)), (fbx, mid + G(10)))
    sh.seg((fbx, mid + G(10)), (u2a.pin("-").x - G(3), mid + G(10)))
    sh.seg((u2a.pin("-").x - G(3), mid + G(10)),
           (u2a.pin("-").x - G(3), u2a.pin("-").y))
    sh.seg((u2a.pin("-").x - G(3), u2a.pin("-").y), u2a.pin("-"))
    sh.seg((fbx, mid + G(2)), (fbx + G(6), mid + G(2)))
    sh.label((fbx + G(6), mid + G(2)), "VREF_P", kind="global")

    # inverter: VREF_P -> -2.5 V
    ix = fbx + G(14)
    iy = mid + G(24)
    r4 = sh.place(R_LIB, "R4", at=(ix + G(12), iy), rot=90, value="10k0")
    sh.seg((ix, iy), r4.pin(1))
    sh.label((ix, iy), "VREF_P", kind="global")
    u2b = sh.place(opamp, refs[1], at=(ix + G(38), iy - G(2)),
                   unit=1 if refs[0] != refs[1] else 2,
                   value=opamp.split(":")[1])
    sh.seg(r4.pin(2), (ix + G(21), iy))
    sh.seg((ix + G(21), iy), u2b.pin("-"))
    r5 = sh.place(R_LIB, "R5", at=(ix + G(38), iy + FB), rot=90, value="10k0")
    sh.seg((ix + G(29), iy), (ix + G(29), iy + FB))
    sh.seg((ix + G(29), iy + FB), r5.pin(1))
    sh.seg(r5.pin(2), (ix + G(46), iy + FB))
    sh.seg((ix + G(46), iy + FB), (ix + G(46), iy - G(2)))
    sh.seg(u2b.pin("out"), (ix + G(52), iy - G(2)))
    sh.label((ix + G(52), iy - G(2)), "VREF_N", kind="global")
    sh.seg(u2b.pin("+"), (ix + G(25), iy - G(4)))
    sh.seg((ix + G(25), iy - G(4)), (ix + G(25), iy + G(16)))
    sh.gnd((ix + G(25), iy + G(16)))

    if not supply:
        return u2a, u2b

    sup = sh.place(opamp, "U2", at=(rx + G(16), mid + G(30)), unit=3,
                  value=opamp.split(":")[1])
    vp, vn = sup.pin("V+"), sup.pin("V-")
    sh.seg(vp, (vp.x, vp.y - STUB))
    sh.rail((vp.x, vp.y - STUB), net=rail, rise=STUB)
    sh.seg(vn, (vn.x, vn.y + STUB))
    sh.rail((vn.x, vn.y + STUB), net="-5V", rise=-STUB)
    c7 = sh.place(C_LIB, "C7", at=(vp.x + G(10), vp.y - STUB + G(3)), rot=0,
                  value="100n")
    sh.seg((vp.x, vp.y - STUB), (vp.x + G(10), vp.y - STUB))
    sh.seg((vp.x + G(10), vp.y - STUB), c7.pin(1))
    c8 = sh.place(C_LIB, "C8", at=(vp.x + G(10), vn.y + STUB - G(3)), rot=0,
                  value="100n")
    sh.seg(c7.pin(2), c8.pin(1))
    sh.seg(c8.pin(2), (vp.x + G(10), vn.y + STUB))
    sh.seg((vn.x, vn.y + STUB), (vp.x + G(10), vn.y + STUB))
    gy = round((c7.pin(2).y + c8.pin(1).y) / 2 / 1.27) * 1.27
    sh.seg((vp.x + G(10), gy), (vp.x + G(16), gy))
    sh.power("power:GND", (vp.x + G(16), gy), rot=270)
    return u2a, u2b



def power_flags(sh, x, y, nets=("+5V", "-5V", "+3V3", "GND")):
    """One PWR_FLAG per supply, in a row.

    Only the nets the board actually carries: a flag on a rail nothing else
    uses is a single-pin net, which is a real ERC violation rather than a
    harmless decoration.  The analog half has no +3V3 and the digital half no
    -5V, so neither gets the full set.
    """
    for i, net in enumerate(nets):
        fx = x + i * G(12)
        sh.power("power:" + net, (fx, y), rot=0)
        sh.seg((fx, y), (fx, y + G(3)))
        sh.power("power:PWR_FLAG", (fx, y + G(3)), rot=180)


def band_power(sh, y, flags=("+5V", "-5V", "+3V3", "GND"),
               pump_x=G(75), ref_x=G(250), flag_x=G(20), ref_opamp=TL072,
               ref_rail="+5V", pump_second=None):
    note_block(sh, (G(16), y - G(16)), "POWER  (Pi +5V -> charge-pump -5V -> "
            "+/-2.5V DAC reference)", size=2.0)

    # -- incoming +5 V, bulk decoupling, and the flags -----------------------
    x = G(20)
    sh.rail((x, y), net="+5V", rise=STUB)
    sh.seg((x, y), (x, y + G(6)))
    c1 = sh.place(CP_LIB, "C1", at=(x, y + G(10)), rot=0, value="470u")
    sh.seg((x, y + G(6)), c1.pin(1))
    c2 = sh.place(C_LIB, "C2", at=(x + G(8), y + G(10)), rot=0, value="100n")
    sh.seg((x, y + G(6)), (x + G(8), y + G(6)))
    sh.seg((x + G(8), y + G(6)), c2.pin(1))
    sh.seg(c1.pin(2), (x, y + G(14)))
    sh.seg(c2.pin(2), (x + G(8), y + G(14)))
    sh.seg((x, y + G(14)), (x + G(8), y + G(14)))
    sh.gnd((x + G(4), y + G(14)))
    note_block(sh, (x - G(4), y + G(19)),
            "Reservoir sits AT the DAC gate: the DAC's mean supply current\n"
            "is proportional to the signal, so this rail must be LOW\n"
            "IMPEDANCE, not filtered by a series R.", size=1.27)

    power_flags(sh, flag_x, y - G(10), flags)

    # -- charge pump: 74HC244, all eight buffers in parallel -------------
    pump = charge_pump(sh, pump_x, y, second=pump_second)

    # -- +/-2.5 V reference, ratiometric off the same +5 V rail --------
    ref = (reference(sh, ref_x, y, opamp=ref_opamp, rail=ref_rail)
           if ref_x is not None else None)
    return {"pump": pump, "ref": ref}

# ============================================================ BAND B: DIGITAL

def clock_divider(sh, dx, y, clk_label="CLK6M", out_labels=True,
                  nc_spares=True, cap_x=None, mclk_label="MCLK"):
    """The 74HC4040 that makes every clock on the board from one 6.144 MHz can.

    Q0 = BCLK 3.072 MHz, Q1 = MCLK 1.536 MHz, Q4 = the 192 kHz charge-pump
    drive and Q6 = LRCLK 48 kHz -- pins 9, 7, 3 and 4, worth stating in pin
    numbers because the divide-by-two stage being called Q0 rather than Q1 is
    an easy off-by-one to wire.

    Everything downstream of it changes on a master-clock falling edge, which
    is what gives the Pi its I2S setup margin; sim_c_clock measures how much
    of that the ripple delay eats.

    The three switches exist for the testbenches, which wire the clock in and
    the outputs onward rather than naming them -- on a bench sheet a source
    sitting next to the pin it drives is a wire, not a long haul, and the
    scorer is right to say so.  Returns the counter, its clock pin, the four
    used output pins by name and the spare output pins.
    """
    u4 = sh.place("4xxx:4040", "U4", at=(dx, y + G(10)), value="74HC4040")
    if clk_label:
        sh.seg(u4.pin(10), (u4.pin(10).x - G(6), u4.pin(10).y))
        sh.label((u4.pin(10).x - G(6), u4.pin(10).y), clk_label, kind="global")
    tie_low(sh, u4.pin(11))                                    # Reset held low
    outs, tips = {}, {}
    for pin, lbl in ((9, "BCLK"), (7, "MCLK"), (3, "PUMP"), (4, "LRCLK")):
        p = u4.pin(pin)
        outs[lbl] = p
        if lbl == "MCLK":
            lbl = mclk_label        # rev D: MCLK_SRC, then R14, then MCLK
        if out_labels:
            sh.seg(p, (p.x + G(8), p.y))
            sh.label((p.x + G(8), p.y), lbl, kind="global")
            tips[lbl] = (p.x + G(8), p.y)
    spares = [u4.pin(pin) for pin in (6, 5, 2, 13, 12, 14, 15, 1)]
    if nc_spares:
        for p in spares:
            sh.nc(p)
    # cap_x moves the decoupling column: a testbench that runs the twelve
    # outputs off to the right needs it out of their way, because two wires
    # crossing get a junction and become one net
    ic_supply(sh, u4, 16, 8, "C11", dx + G(24) if cap_x is None else cap_x)
    note_block(sh, (dx - G(14), y - G(6)),
            "Q0=BCLK 3.072M  Q1=MCLK 1.536M\nQ4=PUMP 192k  Q6=LRCLK 48k",
            size=1.27)
    return {"u": u4, "clk": u4.pin(10), "outs": outs, "spares": spares,
            "tips": tips}



# The blocks below are separate functions because this circuit is drawn three
# times: once as the reference sheet that shows the whole converter, and once
# each for the two halves that are actually milled.  The retiming flip-flops
# and the DAC drive gates sit INSIDE the modulator's feedback path, so they go
# on the analog board with the loop they belong to; everything else that is
# clocked goes on the digital one.  Calling one function from all three sheets
# is the only thing that keeps the halves equal to the whole.

def blk_pierce(sh, ox, y, refs=("Y1", "U9", "R10", "R11", "C16", "C17"),
               spares=True):
    """Pierce oscillator around a 74HC04: the 2-pin crystal replaces the can.

    Textbook shape: the gate on the signal line, R_f looped over it, the
    crystal bridging input to output underneath, a load cap hanging off each
    crystal leg onto one ground rail, and R_s standing between the gate's
    output and the crystal so the pi network filters the edge and the crystal
    is not overdriven.  A second gate squares the output up; the oscillator
    node itself never leaves the block.

    R_s = 2k2 damps the crystal drive AND, with C2, is what stops the gate
    oscillating through the crystal's own 5 pF holder capacitance instead of
    its motional branch -- sim_i_pierce showed 1k lets that parasitic win.
    The gate must be the UNBUFFERED 74HCU04 (pin-identical to 74HC04): a
    buffered gate's three-stage gain sustains the same parasitic at any R_s
    the crystal mode survives.  27 p per side assumes
    the usual CL ~ 18 pF and a few pF of stray -- the exact value only pulls
    the frequency by tens of ppm, which is inaudible.  R_f ~ 1M biases the
    gate into its linear region.  Returns the buffer's output pin.
    """
    yr, yu, yo = refs[0], refs[1], refs[2:]
    y0 = y + G(8)                       # signal row, same as the can's
    g1 = sh.place("74xx:74HC04", yu, at=(ox + G(10), y0), unit=1,
                  value="74HCU04")
    xa, xo = g1.pin(1).x, g1.pin(2).x   # gate input / output columns
    yf = y0 - G(8)                      # feedback row, over the gate --
                                        # G(6) buries R_f's text in U9A's
    yx = y0 + G(6)                      # crystal row
    yc = yx + G(6)                      # load-cap row
    # R_f over the top, a clean rectangular loop
    rf = sh.place(R_LIB, yo[0], at=(ox + G(10), yf), rot=90, value="1M")
    fl, fr = sorted(rf.pins, key=lambda q: q.x)
    sh.seg(g1.pin(1), (xa, yf))
    sh.seg((xa, yf), fl)
    sh.seg(fr, (xo, yf))
    sh.seg((xo, yf), g1.pin(2))
    # R_s drops from the gate output down into the crystal's right leg
    rs = sh.place(R_LIB, yo[1], at=(xo, y0 + G(3)), rot=0, value="2k2")
    st, sb = sorted(rs.pins, key=lambda q: q.y)
    sh.seg(g1.pin(2), st)
    sh.seg(sb, (xo, yx))
    # the crystal bridges the two columns underneath the gate
    x1 = sh.place("Device:Crystal", yr, at=(ox + G(10), yx), value="6.144MHz")
    cl, cr = sorted(x1.pins, key=lambda q: q.x)
    sh.seg(g1.pin(1), (xa, yx))
    sh.seg((xa, yx), cl)
    sh.seg(cr, (xo, yx))
    # one load cap per leg, both onto one rail with a single ground
    yg = yc + G(4)
    for x_, cref in ((xa, yo[2]), (xo, yo[3])):
        c = sh.place(C_LIB, cref, at=(x_, yc), rot=0, value="27p")
        ct, cb = sorted(c.pins, key=lambda q: q.y)
        sh.seg((x_, yx), ct)
        sh.seg(cb, (x_, yg))
    sh.seg((xa, yg), (xo, yg))
    sh.gnd((round((xa + xo) / 2 / 1.27) * 1.27, yg))
    # the buffer: same package, taps the gate output, squares it up
    g2 = sh.place("74xx:74HC04", yu, at=(ox + G(24), y0), unit=2,
                  value="74HCU04")
    sh.seg(g1.pin(2), g2.pin(3))
    if spares:
        # G(18) pitch, exactly like U3's spares: at G(14) the next gate's
        # tie-low bus runs straight through the previous gate's output pin
        # and grounds it
        for i, un in enumerate((3, 4, 5, 6)):
            gx_ = ox + i * G(18)
            g = sh.place("74xx:74HC04", yu, at=(gx_, y + G(40)),
                         unit=un, value="74HCU04")
            li, ri = gate_pins(g, gx_)
            tie_low(sh, *li)
            sh.nc(*ri)
        # low and to the right, between the two spare strips: the selected
        # clock crosses this block at y+G(24), and ic_supply's ground symbol
        # hangs 2.54 below its rail -- put the supply unit any higher and
        # that pin lands exactly ON the clock wire, where the emitter will
        # dutifully junction it
        u9p = sh.place("74xx:74HC04", yu, at=(ox + G(66), y + G(44)),
                       unit=7, value="74HCU04")
        ic_supply(sh, u9p, 14, 7, "C9", u9p.pin(14).x + G(8))
    return g2.pin(4)


def blk_oscillator(sh, ox, y):
    """The 6.144 MHz Pierce oscillator, and the jumper selecting it or GPCLK0.

    Returns the point at which the selected clock leaves the jumper, so the
    buffer downstream can wire to it rather than name it.
    """
    out = blk_pierce(sh, ox, y)

    # J1 sits below the oscillator so its output run clears the pins, and
    # every approach is horizontal: a vertical down a header's pin column
    # shorts every pin it passes.
    j1 = sh.place("Connector_Generic:Conn_01x03", "J1",
                  at=(ox + G(44), y + G(16)), mirror="y", value="CLK SEL")
    far = j1.pin(1).x + G(10)
    sh.seg(out, (far, out.y))
    sh.seg((far, out.y), (far, j1.pin(1).y))
    sh.seg((far, j1.pin(1).y), j1.pin(1))
    # G(8), not G(2): the jumper's "CLK SEL" value text is drawn just right
    # of its pins and a nearer label sits underneath it
    sh.seg(j1.pin(3), (j1.pin(3).x + G(8), j1.pin(3).y))
    sh.label((j1.pin(3).x + G(8), j1.pin(3).y), "GPCLK0", kind="global")
    sh.seg(j1.pin(2), (j1.pin(2).x + G(5), j1.pin(2).y))
    sh.seg((j1.pin(2).x + G(5), j1.pin(2).y), (j1.pin(2).x + G(5), y + G(24)))
    note_block(sh, (ox - G(2), y + G(30)),
            "Jumper 1-2 = crystal Pierce (ps jitter -> ~100 dB floor).\n"
            "Jumper 2-3 = Pi GPCLK0: ~1 ns -> 68 dB floor, the dominant\n"
            "noise source if left there.  Bring-up only.",
            size=1.27)
    return (j1.pin(2).x + G(5), y + G(24))


def blk_clock_buffer(sh, bx, y, sel, detector=None):
    """74HCT132 Schmitt buffer.  `sel` is where blk_oscillator left the clock.

    HCT, not HC, so that a 3.3 V source still meets VIH: the Pi's GPCLK0 is a
    legal input here only because of that.

    `detector` = (input net, output net) turns the first spare gate into an
    inverter -- both inputs on the one net -- so the rev D clock-alive
    detector has a driver of its own instead of loading LRCLK's real edge
    with its pump capacitor.
    """
    u3 = sh.place("74xx:74LS132", "U3", at=(bx, y + G(8)), unit=1,
                  value="74HCT132")
    sh.seg(sel, (u3.pin(1).x - G(4), y + G(24)))
    sh.seg((u3.pin(1).x - G(4), y + G(24)), (u3.pin(1).x - G(4), u3.pin(1).y))
    sh.seg((u3.pin(1).x - G(4), u3.pin(1).y), u3.pin(1))
    sh.seg((u3.pin(1).x - G(4), u3.pin(1).y), (u3.pin(1).x - G(4), u3.pin(2).y))
    sh.seg((u3.pin(1).x - G(4), u3.pin(2).y), u3.pin(2))
    sh.seg(u3.pin(3), (u3.pin(3).x + G(6), u3.pin(3).y))
    sh.label((u3.pin(3).x + G(6), u3.pin(3).y), "CLK6M", kind="global")
    # spare gates get one compact strip rather than a tall stacked column
    for i, un in enumerate((2, 3, 4)):
        gx_ = bx + G(0) + i * G(18)
        g = sh.place("74xx:74LS132", "U3", at=(gx_, y + G(40)),
                     unit=un, value="74HCT132")
        li, ri = gate_pins(g, gx_)
        if detector and i == 0:
            src, dst = detector
            jx = li[0].x - G(4)
            for q in li:
                sh.seg(q, (jx, q.y))
            sh.seg((jx, li[0].y), (jx, li[-1].y))
            sh.seg((jx, li[0].y), (jx - G(4), li[0].y))
            sh.label((jx - G(4), li[0].y), src, kind="global")
            sh.seg(ri[0], (ri[0].x + G(6), ri[0].y))
            sh.label((ri[0].x + G(6), ri[0].y), dst, kind="global")
            continue
        tie_low(sh, *li)
        sh.nc(*ri)
    note_block(sh, (bx - G(4), y + G(50)),
               "spare gates: inputs tied low" if not detector else
               f"U3B buffers {detector[0]} for the clock-alive LED; "
               "other spares tied low", size=1.27)
    u3p = sh.place("74xx:74LS132", "U3", at=(bx + G(20), y + G(8)), unit=5,
                   value="74HCT132")
    ic_supply(sh, u3p, 14, 7, "C10", u3p.pin(14).x + G(10))
    return (u3.pin(3).x + G(6), u3.pin(3).y)



def blk_retime(sh, fx, y, power_at=None):
    """74HC74: both comparators re-clocked onto the master clock.  ANALOG.

    This is the quantiser proper, and it lives on the analog board because it
    closes the modulator loop: comparator -> flip-flop -> DAC gates -> summing
    junction.  Excess loop delay through that path is compensated by k0, and a
    ribbon cable in the middle of it would add delay the coefficient does not
    know about.
    """
    tips = {}
    for i, ch in enumerate(("L", "R")):
        ff = sh.place("74xx:74HC74", "U5", at=(fx, y + G(6) + i * G(30)),
                      unit=i + 1, value="74HC74")
        d, ck = ff.pin("D"), ff.pin("C")
        sh.seg(d, (d.x - G(6), d.y))
        sh.label((d.x - G(6), d.y), f"CMP_{ch}", kind="global")
        tips[f"CMP_{ch}"] = (d.x - G(6), d.y)
        sh.seg(ck, (ck.x - G(6), ck.y))
        sh.label((ck.x - G(6), ck.y), "MCLK", kind="global")
        tips[f"MCLK_{ch}"] = (ck.x - G(6), ck.y)
        q, qn = ff.pin("Q"), ff.pin("~{Q}")
        sh.seg(q, (q.x + G(6), q.y))
        sh.label((q.x + G(6), q.y), f"Q{ch}", kind="global")
        tips[f"Q{ch}"] = (q.x + G(6), q.y)
        sh.seg(qn, (qn.x + G(6), qn.y))
        sh.label((qn.x + G(6), qn.y), f"QN{ch}", kind="global")
        tips[f"QN{ch}"] = (qn.x + G(6), qn.y)
        for pn in ("~{R}", "~{S}"):
            p = ff.pin(pn)
            dy = STUB if p.y > ff.pin("D").y else -STUB
            sh.seg(p, (p.x, p.y + dy))
            sh.seg((p.x, p.y + dy), (p.x + G(5), p.y + dy))
            sh.rail((p.x + G(5), p.y + dy), net="+5V",
                    rise=STUB if dy < 0 else -STUB)
    # `power_at` moves the package's supply unit and its 100n. Beside the
    # flip-flops the cap's run from pin 14 down to pin 7 is a wall the full
    # height of the package, and on the common board every Q has to cross that
    # line to reach the DAC gates. Underneath, it is out of the way.
    u5p = sh.place("74xx:74HC74", "U5", unit=3, value="74HC74",
                   at=power_at or (fx + G(22), y + G(6)))
    ic_supply(sh, u5p, 14, 7, "C12", u5p.pin(14).x + G(10))
    return tips



def blk_retime_ch(sh, fx, y, ch, r, qsig=None, qnsig=None, rail="+5V"):
    """74HC74, ONE PER CHANNEL: this channel's comparator re-clocked on MCLK.

    It sits on the channel board, not on a shared one, because it closes the
    modulator loop: comparator -> flip-flop -> DAC gates -> summing junction.
    The k0 coefficient compensates the LM311's 200 ns and nothing else, so
    that path must not leave the board.  Half the package is spare and is
    tied off rather than left floating.
    """
    tips = {}
    ff = sh.place("74xx:74HC74", r["Uff"], at=(fx, y + G(6)), unit=1,
                  value="74HC74")
    d, ck = ff.pin("D"), ff.pin("C")
    sh.seg(d, (d.x - G(6), d.y))
    sh.label((d.x - G(6), d.y), f"CMP_{ch}", kind="global")
    tips[f"CMP_{ch}"] = (d.x - G(6), d.y)
    sh.seg(ck, (ck.x - G(6), ck.y))
    sh.label((ck.x - G(6), ck.y), "MCLK", kind="global")
    tips["MCLK"] = (ck.x - G(6), ck.y)
    qsig = qsig or f"Q{ch}"
    qnsig = qnsig or f"QN{ch}"
    q, qn = ff.pin("Q"), ff.pin("~{Q}")
    sh.seg(q, (q.x + G(6), q.y))
    sh.label((q.x + G(6), q.y), qsig, kind="global")
    tips[qsig] = (q.x + G(6), q.y)
    sh.seg(qn, (qn.x + G(6), qn.y))
    sh.label((qn.x + G(6), qn.y), qnsig, kind="global")
    tips[qnsig] = (qn.x + G(6), qn.y)
    for pn in ("~{R}", "~{S}"):
        pp = ff.pin(pn)
        dy = STUB if pp.y > d.y else -STUB
        sh.seg(pp, (pp.x, pp.y + dy))
        sh.seg((pp.x, pp.y + dy), (pp.x + G(5), pp.y + dy))
        sh.rail((pp.x + G(5), pp.y + dy), net=rail,
                rise=STUB if dy < 0 else -STUB)
    sp = sh.place("74xx:74HC74", r["Uff"], at=(fx, y + G(30)), unit=2,
                  value="74HC74")
    tie_low(sh, sp.pin("D"), sp.pin("C"))
    for pn in ("~{R}", "~{S}"):
        pp = sp.pin(pn)
        dy = STUB if pp.y > sp.pin("D").y else -STUB
        sh.seg(pp, (pp.x, pp.y + dy))
        sh.seg((pp.x, pp.y + dy), (pp.x + G(5), pp.y + dy))
        sh.rail((pp.x + G(5), pp.y + dy), net=rail,
                rise=STUB if dy < 0 else -STUB)
    sh.nc(sp.pin("Q"), sp.pin("~{Q}"))
    pwr = sh.place("74xx:74HC74", r["Uff"], unit=3, value="74HC74",
                   at=(fx + G(26), y + G(30)))
    ic_supply(sh, pwr, 14, 7, r["Cf"], pwr.pin(14).x + G(10), rail=rail)
    return tips


def blk_dac_gates_ch(sh, gx, y, ch, r, qsig=None, qnsig=None, rail="+5V"):
    """74HC04, ONE PER CHANNEL: the 1-bit DAC drive from Q and /Q.

    These gates ARE the DAC -- their output levels are the reference the
    converter measures against -- so they sit on the channel board beside the
    summing junctions they drive, sharing that board's +5 V and its reservoir
    rather than a rail at the far end of a cable.
    """
    note_block(sh, (gx - G(10), y - G(6)),
            "1-BIT DAC DRIVE\nDACN = /Q, DACP = Q (taken from Q and /Q so the\n"
            "two edges are as close to simultaneous as the parts allow)",
            size=1.27)
    tips = {}
    for i, (src, dst) in enumerate((((qsig or f"Q{ch}"), f"DACN_{ch}"),
                                    ((qnsig or f"QN{ch}"), f"DACP_{ch}"))):
        g = sh.place("74xx:74HC04", r["Udac"], at=(gx, y + G(6) + i * G(10)),
                     unit=i + 1, value="74HC04")
        li, ri = gate_pins(g, gx)
        ip, op = li[0], ri[0]
        sh.seg(ip, (ip.x - G(6), ip.y))
        sh.label((ip.x - G(6), ip.y), src, kind="global")
        tips[src] = (ip.x - G(6), ip.y)
        sh.seg(op, (op.x + G(6), op.y))
        sh.label((op.x + G(6), op.y), dst, kind="global")
        tips[dst] = (op.x + G(6), op.y)
    for i, un in enumerate((3, 4, 5, 6)):
        g = sh.place("74xx:74HC04", r["Udac"],
                     at=(gx + (i % 2) * G(24), y + G(30) + (i // 2) * G(12)),
                     unit=un, value="74HC04")
        li, ri = gate_pins(g, gx + (i % 2) * G(24))
        tie_low(sh, *li)
        sh.nc(*ri)
    pwr = sh.place("74xx:74HC04", r["Udac"], at=(gx + G(56), y + G(6)),
                   unit=7, value="74HC04")
    ic_supply(sh, pwr, 14, 7, r["Cg"], pwr.pin(14).x + G(10), rail=rail)
    return tips


def blk_mux(sh, mx, y):
    """74HC157: L and R interleaved onto one serial data line.  DIGITAL."""
    u6 = sh.place("74xx:74LS157", "U6", at=(mx, y + G(14)), value="74HC157")
    tips = {}
    for pin, lbl in ((1, "MCLK"), (2, "QR"), (3, "QL")):
        p = u6.pin(pin)
        sh.seg(p, (p.x - G(7), p.y))
        sh.label((p.x - G(7), p.y), lbl, kind="global")
        tips[lbl] = (p.x - G(7), p.y)
    sh.seg(u6.pin(4), (u6.pin(4).x + G(7), u6.pin(4).y))
    sh.label((u6.pin(4).x + G(7), u6.pin(4).y), "DIN", kind="global")
    tips["DIN"] = (u6.pin(4).x + G(7), u6.pin(4).y)
    tie_low(sh, u6.pin(15))
    tie_low(sh, *[u6.pin(n) for n in (5, 6, 10, 11, 13, 14)])
    for n in (7, 9, 12):
        sh.nc(u6.pin(n))
    ic_supply(sh, u6, 16, 8, "C13", mx + G(24))
    note_block(sh, (mx - G(16), y - G(6)),
            "MCLK selects: DIN carries R,L,R,L... at 3.072 Mbps.\n"
            "64 BCLK per LRCLK frame = 32 L bits + 32 R bits\n"
            "= exactly one OSR-32 sample per channel.", size=1.27)
    return tips



def blk_dac_gates(sh, gx, y):
    """74HC04: the 1-bit DAC drive, taken from Q and /Q.  ANALOG.

    Inside the loop for the same reason as blk_retime, and additionally
    because these gates ARE the DAC: their output levels are the reference the
    converter measures against, so they share the analog board's +5 V rail and
    its reservoir rather than a rail at the far end of a cable.
    """
    note_block(sh, (gx - G(10), y - G(6)),
            "1-BIT DAC DRIVE\nDACN = /Q, DACP = Q (taken from Q and /Q so the\n"
            "two edges are as close to simultaneous as the parts allow)",
            size=1.27)
    tips = {}
    for i, (src, dst) in enumerate((("QL", "DACN_L"), ("QNL", "DACP_L"),
                                    ("QR", "DACN_R"), ("QNR", "DACP_R"))):
        g = sh.place("74xx:74HC04", "U7", at=(gx, y + G(6) + i * G(10)),
                     unit=i + 1, value="74HC04")
        li, ri = gate_pins(g, gx)
        ip, op = li[0], ri[0]
        sh.seg(ip, (ip.x - G(6), ip.y))
        sh.label((ip.x - G(6), ip.y), src, kind="global")
        tips[src] = (ip.x - G(6), ip.y)
        sh.seg(op, (op.x + G(6), op.y))
        sh.label((op.x + G(6), op.y), dst, kind="global")
        tips[dst] = (op.x + G(6), op.y)
    for i, un in enumerate((5, 6)):
        g = sh.place("74xx:74HC04", "U7", at=(gx + i * G(24), y + G(46)),
                     unit=un, value="74HC04")
        li, ri = gate_pins(g, gx + i * G(24))
        tie_low(sh, *li)
        sh.nc(*ri)
    u7p = sh.place("74xx:74HC04", "U7", at=(gx + G(22), y + G(6)), unit=7,
                   value="74HC04")
    ic_supply(sh, u7p, 14, 7, "C14", u7p.pin(14).x + G(10))
    return tips



def blk_levelshift(sh, lx, y, series=None):
    """74HC4049: 5 V logic down to the Pi's 3.3 V.  DIGITAL.

    `series` maps a signal to a refdes -- {"BCLK": "R12", "LRCLK": "R13"} --
    and puts 475 R (E96, stocked) between that inverter and the Pi.  Bring-up found the
    Pi's I2S pins are OUTPUTS until a stream is first opened (bringup log
    6.3), so until then two push-pull drivers meet on BCLK and LRCLK; the
    resistor limits that contention to a few milliamps and costs nothing at
    3 MHz into a few tens of pF.
    """
    note_block(sh, (lx - G(8), y - G(6)),
            "LEVEL SHIFT to 3.3 V.  74HC4049 tolerates inputs above its own\n"
            "VCC, which is exactly what makes it legal here.  Two inverters\n"
            "per signal so BCLK polarity is preserved -- inverting BCLK would\n"
            "make the Pi sample on the data transition.", size=1.27)
    tips = {}
    for i, sig in enumerate(("BCLK", "LRCLK", "DIN")):
        a = sh.place("4xxx:4049", "U8", at=(lx, y + G(6) + i * G(14)),
                     unit=2 * i + 1, value="74HC4049")
        b = sh.place("4xxx:4049", "U8", at=(lx + G(16), y + G(6) + i * G(14)),
                     unit=2 * i + 2, value="74HC4049")
        la, ra = gate_pins(a, lx)
        lb, rb_ = gate_pins(b, lx + G(16))
        ai, ao = la[0], ra[0]
        bi, bo = lb[0], rb_[0]
        sh.seg(ai, (ai.x - G(6), ai.y))
        sh.label((ai.x - G(6), ai.y), sig, kind="global")
        tips[sig] = (ai.x - G(6), ai.y)
        sh.seg(ao, bi)
        if series and sig in series:
            rs = sh.place(R_LIB, series[sig], at=(bo.x + G(9), bo.y), rot=90,
                          value="475R")
            rl, rr = sorted(rs.pins, key=lambda q: q.x)
            sh.seg(bo, rl)
            sh.seg(rr, (bo.x + G(14), bo.y))
            end = (bo.x + G(14), bo.y)
        else:
            sh.seg(bo, (bo.x + G(6), bo.y))
            end = (bo.x + G(6), bo.y)
        sh.label(end, f"PI_{sig}", kind="global")
        tips["PI_" + sig] = end
    # BELOW the three signal rows, not beside them.  At (lx + G(34), y + G(6))
    # -- where this used to be -- the package body lands exactly where the
    # first PI_ label goes and the label is drawn inside it.
    u8p = sh.place("4xxx:4049", "U8", at=(lx + G(30), y + G(48)), unit=7,
                   value="74HC4049")
    ic_supply(sh, u8p, 1, 8, "C15", u8p.pin(1).x + G(10), rail="+3V3")
    return tips



def blk_pi_header(sh, hx, y):
    """The GPIO header.  DIGITAL -- and the board's only power inlet."""
    # NOT mirrored.  A plain Conn_01x** has its connection points 5.08 mm to
    # the LEFT of the body, so wires leaving leftwards run away from it;
    # mirror="y" moves the pins to the right and every one of these stubs then
    # crosses the connector's own rectangle, taking the pin labels with it.
    j2 = sh.place("Connector_Generic:Conn_01x08", "J2", at=(hx, y + G(14)),
                  value="TO PI GPIO")
    rows = [(1, "+5V", "rail"), (2, "GND", "gnd"), (3, "+3V3", "rail"),
            (4, "PI_BCLK", "lbl"), (5, "PI_LRCLK", "lbl"),
            (6, "PI_DIN", "lbl"), (7, "GPCLK0", "lbl"), (8, "GND", "gnd")]
    # Every stub ends in its symbol or label with NO vertical: on a 2.54 mm
    # pin pitch any riser lands on a neighbour's stub.  The two grounds are the
    # one exception and get a shared bus, run further out than every other stub
    # so it crosses nothing.
    tips = {}
    gnd_x = j2.pin(1).x - G(15)
    gnds = [j2.pin(pin) for pin, n, k in rows if k == "gnd"]
    for p in gnds:
        sh.seg(p, (gnd_x, p.y))
    sh.seg((gnd_x, gnds[0].y), (gnd_x, gnds[-1].y))
    sh.gnd((gnd_x, gnds[-1].y), drop=STUB)
    for pin, name, kind in rows:
        if kind == "gnd":
            continue
        p = j2.pin(pin)
        # rails reach further out than labels: a rail symbol draws its text
        # above the stub end, back towards the pin numbers
        tx = p.x - (G(12) if kind == "rail" else G(8))
        sh.seg(p, (tx, p.y))
        tips[name] = (tx, p.y)
        if kind == "lbl":
            sh.label((tx, p.y), name, kind="global")
        else:
            sh.rail((tx, p.y), net=name, rise=0)
    note_block(sh, (hx - G(12), y + G(32)),
            "Pi pins: 1=+5V(pin2)  2=GND(6)  3=+3V3(1)\n"
            "4=BCLK GPIO18(12)  5=LRCLK GPIO19(35)\n"
            "6=DIN GPIO20(38)   7=GPCLK0 GPIO4(7)  8=GND(39)\n"
            "Pi is I2S SLAVE: this board is the clock master.", size=1.27)
    return tips


# The Pi's 40-pin GPIO header, seen from the board it plugs onto.  Odd pins
# are the row nearer the Pi's centre (3V3 on pin 1), even pins the row along
# the Pi's edge (5V on pin 2).  Only the I2S trio, GPCLK0, both supplies and
# the grounds are wired; the other 24 pins are marked no-connect so ERC does
# not have to guess.
PI40 = {1: "+3V3", 17: "+3V3", 2: "5V", 4: "5V",
        6: "GND", 9: "GND", 14: "GND", 20: "GND", 25: "GND", 30: "GND",
        34: "GND", 39: "GND",
        7: "GPCLK0", 12: "PI_BCLK", 35: "PI_LRCLK", 38: "PI_DIN"}


def blk_pi40_header(sh, hx, y, extra=None, inlet=("FB1", "Device:FerriteBead", "FB")):
    """The Raspberry Pi 4 itself, on a 2x20 socket.  REV C, DIGITAL.

    `extra` maps more pin numbers to net names -- rev D's status LEDs,
    buttons and the HAT ID EEPROM -- and `inlet` names the part between the
    Pi's 5 V pins and +5V (a bead on rev C, a 10 uH choke on rev D).

    The Pi sits UNDER the board HAT-style, plugged into a socket on the
    copper side, and it is also the board's only power inlet: its 5 V pins
    come in through a ferrite bead onto the +5V rail, so the Pi's own
    switching noise meets an impedance before it meets the DAC gates'
    reservoir (bringup log, open item 4).
    """
    j2 = sh.place("Connector_Generic:Conn_02x20_Odd_Even", "J2",
                  at=(hx, y + G(14)), value="RASPBERRY PI 4")
    left = min(p.x for p in j2.pins)
    right = max(p.x for p in j2.pins)
    tips = {}

    # a ground bus down each side, well clear of the label text
    for col, pins in ((left - G(18), (9, 25, 39)),
                      (right + G(18), (6, 14, 20, 30, 34))):
        pp = [j2.pin(n) for n in pins]
        for p in pp:
            sh.seg(p, (col, p.y))
        sh.seg((col, pp[0].y), (col, pp[-1].y))
        sh.gnd((col, pp[-1].y), drop=STUB)

    # both 3V3 pins, straight out to a rail symbol each
    for n in (1, 17):
        p = j2.pin(n)
        sh.seg(p, (p.x - G(6), p.y))
        sh.rail((p.x - G(6), p.y), net="+3V3", rise=0)

    # the 5 V pins share one stub, up and through the bead onto +5V
    p2, p4 = j2.pin(2), j2.pin(4)
    bx = right + G(4)
    sh.seg(p2, (bx, p2.y))
    sh.seg(p4, (bx, p4.y))
    sh.seg((bx, p4.y), (bx, p2.y))
    sh.seg((bx, p2.y), (bx, p2.y - G(4)))
    if extra is not None:
        # rev D names the Pi side of the inlet so the board can give that
        # 100 mA track the supply width; on the corner, text away from it
        sh.label((bx, p4.y), "PI_5V", kind="global")
    fb = sh.place(inlet[1], inlet[0], at=(bx + G(7), p2.y - G(4)),
                  rot=90, value=inlet[2])
    fl, fr = sorted(fb.pins, key=lambda q: q.x)
    sh.seg((bx, p2.y - G(4)), fl)
    sh.seg(fr, (bx + G(14), p2.y - G(4)))
    sh.rail((bx + G(14), p2.y - G(4)), net="+5V", rise=STUB)
    tips["+5V"] = (bx + G(14), p2.y - G(4))

    # the four signals: labels leave leftwards on the odd row, rightwards on
    # the even one, each pointing away from the header
    wired = dict(PI40)
    wired.update(extra or {})
    lefts = [(7, "GPCLK0"), (35, "PI_LRCLK")]
    rights = [(12, "PI_BCLK"), (38, "PI_DIN")]
    for n, net in sorted((extra or {}).items()):
        (lefts if n % 2 else rights).append((n, net))
    for n, net in lefts:
        p = j2.pin(n)
        sh.seg(p, (p.x - G(6), p.y))
        sh.label((p.x - G(6), p.y), net, rot=180, kind="global")
        tips[net] = (p.x - G(6), p.y)
    for n, net in rights:
        p = j2.pin(n)
        sh.seg(p, (p.x + G(6), p.y))
        sh.label((p.x + G(6), p.y), net, kind="global")
        tips[net] = (p.x + G(6), p.y)

    for p in j2.pins:
        if int(p.number) not in wired:
            sh.nc(p)

    note_block(sh, (hx - G(20), y + G(58)),
            "RASPBERRY PI 4 on a 2x20 socket, mounted UNDER the board.\n"
            "1/17=3V3  2/4=5V in (through FB1 onto +5V)  7=GPCLK0 GPIO4\n"
            "12=BCLK GPIO18  35=LRCLK GPIO19  38=DIN GPIO20  even GND\n"
            "Pi is I2S SLAVE: this board is the clock master.", size=1.27)
    return tips


# What crosses between boards, and nothing else.
#
# On a 2xN Odd_Even header the odd pins are the left column and the even pins
# the right, so putting every ground on an odd pin gives a solid ground column
# down one side of the connector and the signals down the other.  That is not
# only a tidier drawing: an IDC ribbon takes conductor n to pin n, so the same
# choice puts a grounded conductor either side of every signal in the cable.
# MCLK is why it matters -- its jitter is what sets this converter's noise
# floor, 20 ps buying a 102 dB floor where 1 ns leaves 68.
#
# Every link is a SHROUDED IDC box header, not a bare pin strip, because these
# rows carry supplies against grounds: plugged in reversed, a bare strip puts
# +5V straight across the ground column.  The shroud's key makes that
# impossible and costs nothing.  Both supplies sit at the ENDS of the signal
# column so their power symbols escape vertically instead of through the
# labels.

def link(*signals):
    """Odd pins all GND, even pins the signals in order.  -> the pin table."""
    out = []
    for k, net in enumerate(signals):
        out.append((2 * k + 1, "GND", "gnd"))
        out.append((2 * k + 2, net, "rail" if net in ("+5V", "-5V") else "lbl"))
    return tuple(out)


# common <-> digital: the master clock out, the two quantiser outputs back,
# and the charge pump's 192 kHz drive.
LINK_DIGITAL = link("+5V", "MCLK", "QL", "QR", "PUMP", "+5V")

# common <-> one channel board: both supplies, both references, and the three
# nets that carry the modulator loop across -- the comparator out, and the
# 1-bit DAC's two drives back into the summing junctions.
def link_channel(ch):
    return link("+5V", "VREF_P", "VREF_N",
                f"CMP_{ch}", f"DACP_{ch}", f"DACN_{ch}", "-5V")


# THE STACKING BUS.  One 2x8 on every board, same pinout and same place, so
# the four boards plug into each other on 11 mm standoffs instead of being
# cabled.  Only eight nets have to cross, which is what keeping each
# modulator loop on its own board bought.
LINK_BUS = link("+5V", "VREF_P", "VREF_N", "MCLK", "PUMP", "QL", "QR", "-5V")

NOTE_BUS = (
    "STACKING BUS  2x8, 2.54 mm.  Every board carries this same connector at\n"
    "the same coordinates; the stack is digital, channel L, channel R, power\n"
    "on 11 mm standoffs.  Odd pins are all GND, so every signal has a\n"
    "grounded neighbour either side -- which is what MCLK needs, its jitter\n"
    "being what sets this converter's noise floor.")


def stack_bus(sh, x, y, ref):
    """The stacking bus: ONE 2x8 position per board, at the same coordinates.

    It has to be one position, not a socket and a header side by side.  A
    middle board must present a socket UPWARDS to the board above and pins
    DOWNWARDS to the board below, and stacking identical boards puts the one
    directly over the other -- so they must share an XY, which two separate
    parts cannot do.  What goes in the holes is a build choice: a plain
    socket on the top board, a long-pin header on the bottom one, and a
    pass-through stacking header on the two in the middle.  All three are the
    same sixteen pads on 2.54 mm, so the artwork does not care.
    """
    return interconnect(sh, x, y, ref, LINK_BUS, NOTE_BUS, value="2x8 BUS")


def q_select(sh, x, y, ref):
    """Which bus line this channel drives.

    Both channel boards are the same copper, so nothing etched on the board
    can say which channel it is.  The shunt does: 1-2 makes it left, 2-3
    right.  The netlist is identical either way -- the choice is deliberately
    NOT in the copper, which is what lets one artwork be milled twice.
    """
    j = sh.place("Connector_Generic:Conn_01x03", ref, at=(x, y), value="Q SEL")
    for pin, net in ((1, "QL"), (2, "Q_OUT"), (3, "QR")):
        pp = j.pin(pin)
        sh.seg(pp, (pp.x + G(8), pp.y))
        sh.label((pp.x + G(8), pp.y), net, kind="global")
    note_block(sh, (x - G(6), y + G(12)),
            "Q SELECT.  Shunt 1-2 = LEFT, 2-3 = RIGHT.  The two channel\n"
            "boards are one artwork; this shunt is the only thing that\n"
            "differs between them, so mark the board L or R when you fit it.",
            size=1.27)
    return j


def interconnect(sh, x, y, ref, pins, note, value=None):
    """One 2xN header wired to `pins`, drawn the same way every time.

    `note` may be None, for the second of a pair that shares one caption.
    `value` picks the footprint where two connectors share a symbol.
    """
    n = len(pins) // 2
    lib = f"Connector_Generic:Conn_02x{n:02d}_Odd_Even"
    j = sh.place(lib, ref, at=(x, y + G(14)), value=value or f"2x{n} IDC")
    tips = {}

    # the grounds share one bus, set well clear of the pin column: a vertical
    # run down a header's own pins shorts every pin it passes
    gnds = [j.pin(p) for p, net, kind in pins if kind == "gnd"]
    gx = gnds[0].x - G(8)
    for pin in gnds:
        sh.seg(pin, (gx, pin.y))
    sh.seg((gx, gnds[0].y), (gx, gnds[-1].y))
    sh.gnd((gx, gnds[-1].y), drop=STUB)

    # the supplies leave UPWARDS and DOWNWARDS rather than out through the
    # label column: they are the top and bottom of the even row, so each
    # escapes into clear sheet.  A rail symbol on a plain stub would draw its
    # text across the signal label two rows away.
    rails = [(j.pin(p), net) for p, net, kind in pins if kind == "rail"]
    rx = rails[0][0].x + G(4)
    for k, (pin, net) in enumerate(rails):
        dy = -G(6) if k == 0 else G(6)
        sh.seg(pin, (rx, pin.y))
        sh.seg((rx, pin.y), (rx, pin.y + dy))
        sh.rail((rx, pin.y + dy), net=net, rise=STUB if dy < 0 else -STUB)
        tips[net] = (rx, pin.y + dy)

    for p, net, kind in pins:
        if kind != "lbl":
            continue
        pin = j.pin(p)
        tx = pin.x + G(8)
        sh.seg(pin, (tx, pin.y))
        tips[net] = (tx, pin.y)
        sh.label((tx, pin.y), net, kind="global")

    if note:
        note_block(sh, (x - G(10), y + G(14) + G(2) * n + G(10)), note,
                   size=1.27)
    return tips


def band_digital(sh, y, pi40=False, hat=None, detector=None,
                 mclk_label="MCLK", inlet=("FB1", "Device:FerriteBead", "FB")):
    """Every clocked block on one band: the reference sheet's arrangement.

    `pi40` swaps the 8-way pigtail for the Pi's own 40-pin socket and puts
    the 470 R series resistors in BCLK and LRCLK -- the rev C board.  The
    rest are rev D: `hat` wires more of the Pi's pins, `detector` gives the
    clock-alive LED its own gate, `mclk_label` lets a damping resistor sit
    between the divider and MCLK, `inlet` picks the 5 V inlet part.
    """
    note_block(sh, (G(16), y - G(16)),
            "CLOCK AND DIGITAL  (6.144 MHz -> /2 BCLK 3.072M, /4 MCLK 1.536M, "
            "/128 LRCLK 48k;  L and R interleaved onto one DIN)", size=2.0)
    sel = blk_oscillator(sh, G(18), y)
    # G(104) is far enough right that the buffer's input riser clears every
    # stub on the clock-select jumper and the Pierce's supply unit
    blk_clock_buffer(sh, G(104), y, sel, detector=detector)
    clock_divider(sh, G(156), y, mclk_label=mclk_label)
    blk_mux(sh, G(214), y)
    if pi40:
        blk_levelshift(sh, G(270), y, series={"BCLK": "R12", "LRCLK": "R13"})
        blk_pi40_header(sh, G(352), y, extra=hat, inlet=inlet)
    else:
        blk_levelshift(sh, G(270), y)
        blk_pi_header(sh, G(340), y)


# ====================================================== BANDS C/D: MODULATORS

def front_end(sh, jx, y, r, ch, jack=True, pot=True):
    """Line input: DC block, anti-alias RC and the level trimmer.

    `jack=False` leaves the connector off so a testbench can drive the same
    network from a source.  `pot=False` draws the trimmer as its two halves at
    FULL rotation, which is the setting every number in docs/design-notes.md
    assumes -- and, unlike a potentiometer symbol, something a SPICE deck can
    actually solve, because no one ships a model for a three-terminal pot.

    Returns the part whose pin 2 is the wiper.
    """
    cin = sh.place(C_LIB, r["Cin"], at=(jx + G(12), y), rot=90, value="2u2")
    if not jack:
        # no connector: the caller drives (jx, y) instead
        sh.seg((jx, y), cin.pin(1))
    if jack:
        j = sh.place("Connector:Screw_Terminal_01x02", r["J"], at=(jx, y),
                     mirror="y", value=f"LINE IN {ch}")
        sh.seg(j.pin(1), cin.pin(1))
        sh.seg(j.pin(2), (j.pin(2).x + G(3), j.pin(2).y))
        sh.seg((j.pin(2).x + G(3), j.pin(2).y),
               (j.pin(2).x + G(3), y + G(10)))
        sh.gnd((j.pin(2).x + G(3), y + G(10)))

    raa = sh.place(R_LIB, r["Raa"], at=(jx + G(24), y), rot=90, value="1k00")
    sh.seg(cin.pin(2), raa.pin(1))
    caa = sh.place(C_LIB, r["Caa"], at=(jx + G(32), y + G(6)), rot=0,
                   value="1n5")
    sh.seg(raa.pin(2), (jx + G(32), y))
    sh.seg((jx + G(32), y), caa.pin(1))
    sh.seg(caa.pin(2), (jx + G(32), y + G(12)))
    sh.gnd((jx + G(32), y + G(12)))

    if pot:
        rv = sh.place("Device:R_Potentiometer_Trim", r["RV"],
                      at=(jx + G(42), y + G(3)), value="47k")
        sh.seg((jx + G(32), y), (rv.pin(1).x, y))
        sh.seg((rv.pin(1).x, y), rv.pin(1))
        sh.seg(rv.pin(3), (rv.pin(3).x, y + G(12)))
        sh.gnd((rv.pin(3).x, y + G(12)))
    else:
        rv = sh.place(R_LIB, r["RV"], at=(jx + G(42), y + G(2)), rot=0,
                      value="1R00")
        low = sh.place(R_LIB, r["RVb"], at=(jx + G(42), y + G(10)), rot=0,
                       value="47k0")
        sh.seg((jx + G(32), y), (rv.pin(1).x, y))
        sh.seg((rv.pin(1).x, y), rv.pin(1))
        sh.seg(rv.pin(2), low.pin(1))
        sh.seg(low.pin(2), (low.pin(2).x, y + G(16)))
        sh.gnd((low.pin(2).x, y + G(16)))
    note_block(sh, (jx + G(4), y - G(14)),
            "2u2 + 47k -> 1.5 Hz HP;  1k + 1n5 -> 106 kHz anti-alias.\n"
            "Trim sets full scale: 3.5 Vpk (2.5 Vrms) at wiper max, and only\n"
            "attenuates from there.  Overload is 0.70 FS = 1.7 Vrms in.\n"
            f"For a quieter source drop {r['Rin']}: FS = 2.5 V x "
            f"{r['Rin']}/{r['Rd1']}.",
            size=1.27)
    return rv


def quantiser(sh, XC, y, r, ch, v3=None, rows_labelled=True, rail="+5V"):
    """LM311 on a single supply, its four-resistor summing node and pull-up.

    The node sums the third integrator through Rs, the DAC through Rk0 -- the
    excess-loop-delay compensation -- and VREF_P through Rsh, with Rb to +5 V
    balancing it so the threshold lands exactly on VREF_P when the DAC sits at
    its mean.  `v3` is the third integrator, routed over the top of the
    resonator inverter into row 0 when given.

    `rows_labelled=False` leaves the row labels off so a testbench can wire
    its own sources straight onto the rows.

    Returns the row entry points by role.
    """
    cy = y
    rows = [(None, r["Rs"], "22k1"),
            (f"DACP_{ch}", r["Rk0"], "165k"),
            ("VREF_P", r["Rsh"], "22k1")]
    n = len(rows) + 1
    y_s = cy + (n - 1) * COL / 2.0
    y_s = round(y_s / 1.27) * 1.27
    bus_x = XC + G(21)
    cmp_u = sh.place("Comparator:LM311", r["Ucmp"], at=(XC + G(38), y_s - G(2)),
                     value="LM311")
    for i, (lbl, rref, rval) in enumerate(rows):
        ry = cy + i * COL
        rr = sh.place(R_LIB, rref, at=(XC + G(12), ry), rot=90, value=rval)
        sh.seg((XC, ry), rr.pin(1))
        sh.seg(rr.pin(2), (bus_x, ry))
        if lbl and rows_labelled:
            sh.label((XC, ry), lbl, kind="global")
    # the +5 V bias leg: equal to Rs, which is what centres the threshold
    ry = cy + 3 * COL
    rb = sh.place(R_LIB, r["Rb"], at=(XC + G(12), ry), rot=90, value="22k1")
    sh.seg((XC, ry), rb.pin(1))
    sh.rail((XC, ry), net=rail, rise=0)
    sh.seg(rb.pin(2), (bus_x, ry))
    sh.seg((bus_x, cy), (bus_x, ry))
    sh.seg((bus_x, y_s), cmp_u.pin(3))
    # + input to the same +2.5 V the summing node is balanced about
    pp = cmp_u.pin(2)
    sh.seg(pp, (pp.x - G(5), pp.y))
    sh.seg((pp.x - G(5), pp.y), (pp.x - G(5), cy - G(8)))
    sh.seg((pp.x - G(5), cy - G(8)), (pp.x - G(12), cy - G(8)))
    plus_pt = (pp.x - G(12), cy - G(8))
    if rows_labelled:
        sh.label(plus_pt, "VREF_P", kind="global")
    # supplies: single +5 V, both grounds down
    v8 = cmp_u.pin(8)
    sh.seg(v8, (v8.x, v8.y - G(6)))
    sh.rail((v8.x, v8.y - G(6)), net=rail, rise=STUB)
    for pn in (1, 4):
        p = cmp_u.pin(pn)
        sh.seg(p, (p.x, p.y + G(6)))
    sh.seg((cmp_u.pin(1).x, cmp_u.pin(1).y + G(6)),
           (cmp_u.pin(4).x, cmp_u.pin(4).y + G(6)))
    sh.gnd((cmp_u.pin(4).x, cmp_u.pin(4).y + G(6)))
    sh.nc(cmp_u.pin(5), cmp_u.pin(6))
    # open-collector output, pulled up, out to the flip-flop
    o = cmp_u.pin(7)
    sh.seg(o, (o.x + G(8), o.y))
    rpu = sh.place(R_LIB, r["Rpu"], at=(o.x + G(8), o.y - G(8)), rot=0,
                   value="2k21")
    sh.seg((o.x + G(8), o.y), rpu.pin(2))
    sh.seg(rpu.pin(1), (o.x + G(8), o.y - G(14)))
    sh.rail((o.x + G(8), o.y - G(14)), net=rail, rise=STUB)
    sh.seg((o.x + G(8), o.y), (o.x + G(14), o.y))
    sh.label((o.x + G(14), o.y), f"CMP_{ch}", kind="global")
    note_block(sh, (XC - G(6), y - G(16)),
            "QUANTISER  (LM311 + retiming D-FF)\n"
            f"{r['Rk0']} is the excess-loop-delay compensation: without it the\n"
            "LM311's 200 ns costs 8 dB and most of the overload margin.\n"
            f"{r['Rb']} = {r['Rs']} is what centres the threshold on VREF_P.",
            size=1.27)

    # V3 also feeds the comparator: over the top, clear of the inverter
    if v3 is not None:
        top_y = y - G(10)
        sh.seg(v3["out"], (v3["out"][0] + G(2), v3["y_out"]))
        sh.seg((v3["out"][0] + G(2), v3["y_out"]),
               (v3["out"][0] + G(2), top_y))
        sh.seg((v3["out"][0] + G(2), top_y), (XC - G(4), top_y))
        sh.seg((XC - G(4), top_y), (XC - G(4), cy))
        sh.seg((XC - G(4), cy), (XC, cy))
    return {"v3": (XC, cy), "dacp": (XC, cy + COL), "vrefp": (XC, cy + 2 * COL),
            "plus": plus_pt, "u": cmp_u, "out": (o.x + G(14), o.y)}



def modulator(sh, ch, y, refs, qsig=None, qnsig=None, rail="+5V",
              int_labels=False):
    """One complete channel. `refs` maps role -> refdes so L and R differ.

    `rail` is the positive supply for everything in the loop -- the op-amps,
    the comparator's bias and pull-up, and the DAC gates whose supply IS
    the reference (rev D: +5VA).  `int_labels` names the three integrator
    outputs INT1..3_ch so the clip detector and the test-point header can
    reach them; the labels sit on the elbow corners, where nothing else is.
    """
    r = refs
    # kept short on purpose: a longer title overruns INTEGRATOR 1's caption
    note_block(sh, (G(16), y - G(26)),
               f"CHANNEL {ch}  -  3rd-order CT delta-sigma, fs 1.536 MHz, "
               f"OSR 32", size=2.0)

    # -- input: coupling, anti-alias, level trim -----------------------------
    jx = G(16)
    pot = front_end(sh, jx, y, r, ch)

    # -- three integrators ---------------------------------------------------
    X1, X2, X3 = G(76), G(136), G(196)
    i1 = summing_stage(sh, X1, y, [(None, r["Rin"], "20k5"),
                               (f"DACN_{ch}", r["Rd1"], "14k7"),
                               ("VREF_N", r["Ro1"], "14k7")],
                       r["Ua"], 1, "C", r["C1"], "220p", opamp=TL072,
                       title="INTEGRATOR 1  (a1 = 0.247)")
    wpr = pot.pin(2)                       # wiper sits 3.81 below the top pin
    sh.seg(wpr, (wpr.x + G(4), wpr.y))
    sh.seg((wpr.x + G(4), wpr.y), (wpr.x + G(4), y))
    sh.seg((wpr.x + G(4), y), (X1, y))

    i2 = summing_stage(sh, X2, y, [(None, r["R2"], "10k5"),
                               (f"DACP_{ch}", r["Rd2"], "13k0"),
                               ("VREF_N", r["Ro2"], "13k0"),
                               (None, r["Rg"], "255k")],
                       r["Ua"], 2, "C", r["C2"], "220p", opamp=TL072,
                       title="INTEGRATOR 2  (a2 = 0.321, + resonator)")
    elbow(sh, i1["out"], (X2, y), X2 - G(4))

    i3 = summing_stage(sh, X3, y, [(None, r["R3"], "5k90"),
                               (f"DACN_{ch}", r["Rd3"], "8k25"),
                               ("VREF_N", r["Ro3"], "8k25")],
                       r["Ub"], 1, "C", r["C3"], "220p", opamp=TL072,
                       title="INTEGRATOR 3  (a3 = 0.611)")
    elbow(sh, i2["out"], (X3, y), X3 - G(4))

    # -- resonator inverter: -V3 back into integrator 2 ----------------------
    XI = G(256)
    inv = summing_stage(sh, XI, y, [(None, r["Ri"], "10k0")],
                        r["Ub"], 2, "R", r["Rf"], "10k0", opamp=TL072,
                        title="RESONATOR INVERTER  (g = 0.0297)")
    elbow(sh, i3["out"], (XI, y), XI - G(4))
    if int_labels:
        for k, (blk, nx) in enumerate(((i1, X2), (i2, X3), (i3, XI)), 1):
            sh.label((nx - G(4), blk["y_out"]), f"INT{k}_{ch}", rot=90,
                     kind="global")

    # return path, right to left along the bottom, up into integrator 2 row 4
    ret_y = y + G(46)
    ox, oy = inv["out"]
    sh.seg((ox, oy), (ox, ret_y))
    sh.seg((ox, ret_y), (X2 - G(2), ret_y))
    sh.seg((X2 - G(2), ret_y), (X2 - G(2), y + 3 * COL))
    sh.seg((X2 - G(2), y + 3 * COL), (X2, y + 3 * COL))

    # -- comparator ----------------------------------------------------------
    quantiser(sh, G(320), y, r, ch, v3=i3, rail=rail)

    # -- the rest of the loop, on this board: retime, then drive the DAC -----
    # Q/QN and DACP/DACN carry between these two by global label rather than
    # by wire; on this sheet they are a row apart, and a wire would have to
    # cross the whole return path to get there.
    blk_retime_ch(sh, G(316), y + G(56), ch, r, qsig, qnsig, rail=rail)
    blk_dac_gates_ch(sh, G(150), y + G(56), ch, r, qsig, qnsig, rail=rail)

    # -- the two TL072 package supplies --------------------------------------
    # Two duals rather than one quad: seventeen resistors cannot all reach the
    # perimeter of a single 19 mm package when nothing passes between DIP
    # pins, so the integrator pairs get a package each and a cluster each.
    # G(36) apart, not G(26): each block reaches STUB past its rail symbol
    # both ways, so at 26 the upper one's -5V stub meets the lower one's +5V
    # and the two rails merge. Every geometry check still passed -- the
    # netlist simply had no -5V net left at all.
    opamp_supply(sh, r["Ua"], (G(392), y + G(6)), r["Ca"], r["Cb"], rail=rail)
    opamp_supply(sh, r["Ub"], (G(392), y + G(42)), r["Cd"], r["Ce"], rail=rail)
    ccmp = sh.place(C_LIB, r["Cc"], at=(G(430), y + G(6)), rot=0, value="100n")
    sh.seg(ccmp.pin(1), (G(430), y + G(2)))
    sh.rail((G(430), y + G(2)), net=rail, rise=STUB)
    sh.gnd(ccmp.pin(2), drop=STUB)


def refs_for(ch, n):
    def k(p):
        return f"{p}{n}"
    return {"J": k("J"), "Cin": k("C"), "Caa": f"C{n+1}", "Raa": k("R"),
            "RV": k("RV"), "Ua": k("U"), "Ucmp": f"U{n+1}",
            "Jq": f"J{n+1}",
            "Ub": f"U{n+2}", "Uff": f"U{n+3}", "Udac": f"U{n+4}",
            "Rin": f"R{n+1}", "Rd1": f"R{n+2}", "Ro1": f"R{n+3}",
            "R2": f"R{n+4}", "Rd2": f"R{n+5}", "Ro2": f"R{n+6}",
            "Rg": f"R{n+7}", "R3": f"R{n+8}", "Rd3": f"R{n+9}",
            "Ro3": f"R{n+10}", "Ri": f"R{n+11}", "Rf": f"R{n+12}",
            "Rs": f"R{n+13}", "Rk0": f"R{n+14}", "Rsh": f"R{n+15}",
            "Rb": f"R{n+16}", "Rpu": f"R{n+17}",
            "C1": f"C{n+2}", "C2": f"C{n+3}", "C3": f"C{n+4}",
            "Ca": f"C{n+5}", "Cb": f"C{n+6}", "Cc": f"C{n+7}",
            "Cd": f"C{n+8}", "Ce": f"C{n+9}", "Cf": f"C{n+10}",
            "Cg": f"C{n+11}"}


# ============================================================== FOOTPRINTS
#
# Every part is through-hole, and the copper is isolation-milled with an 0.8 mm
# flat end mill, so 0.8 mm is a hard floor on every pad-to-pad gap: the tool
# cannot enter anything narrower, and a gap it cannot enter ships as a short.
# Each pick below was measured against that floor with the audit in
# ../sim/../tools -- the numbers are in vinyl_adc.kicad_dru. Only the 2.54 mm
# pin headers land under the 0.85 mm netclass clearance, at 0.84 mm, and they
# get a documented DRC exception rather than a lower global clearance.
#
# Assigned here rather than in the GUI because this script owns the schematic:
# regenerating it would otherwise wipe every footprint field.

FP_DIP = "Package_DIP:DIP-{}_W7.62mm_LongPads"      # LongPads: the mill wants
                                                    # the bigger annular ring
FOOTPRINTS = {
    "Device:R": "Resistor_THT:R_Axial_DIN0207_L6.3mm_D2.5mm_P7.62mm_Horizontal",
    "Device:D_Schottky": "Diode_THT:D_DO-41_SOD81_P10.16mm_Horizontal",
    # The level trim is NOT on the board. It is panel-mounted in the printed
    # enclosure and wired back to these three pads, so what the board carries
    # is a 3-way header -- RIGHT-ANGLE, because a vertical one with a Dupont
    # housing pushed onto it stands ~13 mm and the stack only allows ~9.
    "Device:R_Potentiometer_Trim":
        "Connector_PinHeader_2.54mm:PinHeader_1x03_P2.54mm_Horizontal",
    "Comparator:LM311": FP_DIP.format(8),
    "Amplifier_Operational:TL072": FP_DIP.format(8),
    "Amplifier_Operational:LM358": FP_DIP.format(8),
    # rev C: the Pi's 40-pin header, a socket on the copper side; a bead on a
    # lead for the 5 V inlet, same axial footprint family as the resistors
    "Connector_Generic:Conn_02x20_Odd_Even":
        "Connector_PinSocket_2.54mm:PinSocket_2x20_P2.54mm_Vertical",
    "Device:FerriteBead":
        "Inductor_THT:L_Axial_L7.0mm_D3.3mm_P10.16mm_Horizontal_Fastron_MICC",
    "Amplifier_Operational:TL074": FP_DIP.format(14),
    # a DIP-8 SOCKET footprint, not Oscillator:Oscillator_DIP-8: the can is
    # socketed like every other IC here, and a socket wants all eight pads
    # even though the oscillator only uses 1/4/5/8.  Kept for the plug-in
    # oscillator module, which fills exactly that socket.
    "Oscillator:CXO_DIP8": FP_DIP.format(8),
    # 0.8 mm drill matches the shop's bits; the 4.88 mm pin gap clears the
    # end mill with 3 mm to spare
    "Device:Crystal": "Crystal:Crystal_HC49-U_Vertical",
    "74xx:74HC04": FP_DIP.format(14),
    "74xx:74HC74": FP_DIP.format(14),
    "74xx:74LS132": FP_DIP.format(14),      # fitted as 74HCT132
    "74xx:74LS157": FP_DIP.format(16),      # fitted as 74HC157
    "4xxx:4040": FP_DIP.format(16),         # fitted as 74HC4040
    "4xxx:4049": FP_DIP.format(16),         # fitted as 74HC4049
    "74xx:74HC244": FP_DIP.format(20),
    "Connector_Generic:Conn_01x03":
        "Connector_PinHeader_2.54mm:PinHeader_1x03_P2.54mm_Vertical",
    "Connector_Generic:Conn_01x08":
        "Connector_PinHeader_2.54mm:PinHeader_1x08_P2.54mm_Vertical",
    # shrouded and keyed, so the board-to-board ribbon cannot go in backwards
    # and put +5V across the ground column
    "Connector_Generic:Conn_02x08_Odd_Even":
        "Connector_PinHeader_2.54mm:PinHeader_2x08_P2.54mm_Vertical",
    "Connector_Generic:Conn_02x06_Odd_Even":
        "Connector_IDC:IDC-Header_2x06_P2.54mm_Vertical",
    "Connector_Generic:Conn_02x07_Odd_Even":
        "Connector_IDC:IDC-Header_2x07_P2.54mm_Vertical",
    # KiCad 10 deleted the bornier terminals; vendored into lib/ and registered
    # in the project fp-lib-table, which KiCad reads at PROJECT load
    "Connector:Screw_Terminal_01x02":
        "TerminalBlock:TerminalBlock_bornier-2_P5.08mm",
}

# Capacitors need the value as well as the symbol: a 2u2 film cap and a 220 pF
# disc share Device:C and are nothing like the same part.
# The two bus connectors share one symbol and need different footprints --
# a socket facing up, a long-pin header reaching down -- so they are picked
# by VALUE, which is the only thing that tells them apart.
FOOTPRINTS_V = {
    # Socket, long-pin header and pass-through stacking header are all the
    # same sixteen pads; the footprint is the header one for all of them.
    "2x8 BUS": "Connector_PinHeader_2.54mm:PinHeader_2x08_P2.54mm_Vertical",
}

FOOTPRINTS_C = {
    "2u2": "Capacitor_THT:C_Rect_L11.0mm_W6.3mm_P10.00mm_MKT",
    "470u": "Capacitor_THT:CP_Radial_D10.0mm_P5.00mm",
    "220u": "Capacitor_THT:CP_Radial_D8.0mm_P3.50mm",
    "10u": "Capacitor_THT:CP_Radial_D8.0mm_P3.50mm",
}
FP_DISC = "Capacitor_THT:C_Disc_D5.0mm_W2.5mm_P5.00mm"   # 100n, 1n5, 220p


def footprint_for(part):
    """The footprint for one placed symbol, or "" for power symbols."""
    if part.lib_id.startswith("power:"):
        return ""
    if part.lib_id in ("Device:C", "Device:C_Polarized"):
        return FOOTPRINTS_C.get(part.value, FP_DISC)
    if part.value in FOOTPRINTS_V:
        return FOOTPRINTS_V[part.value]
    return FOOTPRINTS.get(part.lib_id, "")


def assign_footprints(sh):
    """Stamp the footprint field on every placed symbol before emit.

    Returns the refs left without one, which must be empty for anything that
    is going on copper.
    """
    missing = []
    for part in sh.parts:
        fp = footprint_for(part)
        part.footprint = fp
        if not fp and not part.lib_id.startswith("power:"):
            missing.append(f"{part.ref} ({part.lib_id})")
    return sorted(set(missing))


# ===================================================================== build
#
# Every block function above takes the sheet as its first argument so the SPICE
# testbenches in ../sim can draw the SAME blocks. A bench that wires a stage
# differently from the board proves nothing about the board, and the only way
# to guarantee they agree is to call one function from both.

def write_project(sch_path, sheet_uuid):
    """Emit the .kicad_pro alongside the sheet.

    Two things here are load-bearing:

    * every netclass needs `wire_width`.  KiCad 10 applies the netclass wire
      width to every wire on the sheet and a MISSING key resolves to zero, so
      the drawing renders as a page of invisible wires and vanished junction
      dots while the netlist and ERC stay perfectly correct.
    * `sheets` must name the schematic's own root uuid.  If the project claims
      a different one, KiCad resolves symbols against the project's path, finds
      no instance data and drops them out of connectivity -- ERC then reports
      dozens of unconnected pins on a file kicad-cli reads as flawless.

    An EXISTING .kicad_pro is merged into, never replaced.  Once the PCB phase
    starts, that file is shared: KiCad-Autoplace stamps the fabrication
    profile's clearance and track width into it on every run, and KiCad itself
    fills in board design settings, plot options and stackup.  Rewriting it
    from this dictionary would throw all of that away every time the schematic
    was regenerated -- and the loss is silent, because the schematic side would
    still be perfectly correct.
    """
    import json
    pro = os.path.splitext(sch_path)[0] + ".kicad_pro"
    doc = {
        "board": {"design_settings": {"rules": {"min_clearance": 0.85}}},
        "boards": [],
        "libraries": {"pinned_footprint_libs": [], "pinned_symbol_libs": []},
        "meta": {"filename": os.path.basename(pro), "version": 3},
        "net_settings": {
            "classes": [{
                "name": "Default",
                "bus_width": 12.0,
                "wire_width": 6.0,
                "line_style": 0,
                # the `cnc` fabrication profile's numbers -- 0.8 mm end
                # mill plus ~0.025 mm of margin either side of the cut.
                # KiCad-Autoplace stamps these into the .kicad_pro on every
                # run anyway; setting them here means the GUI agrees before
                # the first run rather than after it.
                "clearance": 0.85,
                "track_width": 1.0,
                "via_diameter": 0.8,
                "via_drill": 0.4,
                "schematic_color": "rgba(0, 0, 0, 0.000)",
                "pcb_color": "rgba(0, 0, 0, 0.000)",
            }],
            "meta": {"version": 4},
        },
        "schematic": {
            "drawing": {
                "default_line_thickness": 6.0,
                "default_text_size": 50.0,
                "field_names": [],
                "intersheets_ref_show": False,
                "label_size_ratio": 0.375,
                "pin_symbol_size": 25.0,
                "text_offset_ratio": 0.15,
            },
            "meta": {"version": 1},
        },
        "sheets": [[sheet_uuid, "Root"]],
        "text_variables": {},
    }
    if os.path.exists(pro):
        with open(pro, encoding="utf-8") as f:
            have = json.load(f)
        doc = _merge_project(have, doc)
        what = "updated"
    else:
        what = "wrote"
    with open(pro, "w", encoding="utf-8") as f:
        json.dump(doc, f, indent=2)
    print(what, os.path.normpath(pro))


def _merge_project(have, want):
    """Fold the schematic's required keys into an existing project file.

    Only the keys this script owns are forced: the root-sheet uuid and the
    netclass drawing widths.  Everything else the board phase put there --
    design settings, stackup, plot options, and the fabrication profile's
    clearance and track width -- is left exactly as found.
    """
    out = dict(have)
    out["sheets"] = want["sheets"]
    out.setdefault("schematic", {}).update(want["schematic"])
    classes = out.setdefault("net_settings", {}).setdefault("classes", [])
    if not classes:
        classes.append({"name": "Default"})
    for cls in classes:
        for key in ("wire_width", "bus_width", "line_style"):
            cls.setdefault(key, want["net_settings"]["classes"][0][key])
    return out


# ============================================= THE THREE SHEETS THIS EMITS
#
# The reference sheet is the whole converter on one page: it is what the
# testbenches link back to, and what the split is checked against.  It is NOT
# what gets milled.  Routed as one single-sided board it came out needing 45
# hand-soldered wire bridges, because one copper layer with a ground plane on
# it has no room left for a second net that has to reach everywhere.
#
# So it is cut in the one place the circuit is genuinely narrow: four signals
# and a supply.  What decides where the cut goes is the modulator's feedback
# path -- comparator -> flip-flop -> DAC gates -> summing junction -- whose
# delay is compensated by the coefficient k0.  Put a ribbon cable in the middle
# of that and k0 is wrong by an amount nothing on the board knows about, so the
# flip-flops and the DAC gates stay with the analog half despite being 74HC
# logic.  The clock generator, the interleave mux and the level shift have no
# such constraint and travel with the Pi header.

def board_full(sh):
    """The reference: the entire converter on one A2 sheet."""
    band_power(sh, G(27))
    band_digital(sh, G(109))
    modulator(sh, "L", G(200), refs_for("L", 20))
    modulator(sh, "R", G(310), refs_for("R", 60))
    return sim_index(sh, G(150), G(56))


def board_rev_c(sh):
    """REV C: the whole converter on ONE 4-layer board, fabricated.

    The reference sheet's own arrangement -- the split existed only because
    nothing passes between DIP pins on the milled process, and a fab with a
    ground plane and vias removes that.  Three things differ from the
    reference: U2 is the LM358 the bench needed, the Pi plugs straight in on
    its 40-pin header (and powers the board through a bead), and BCLK/LRCLK
    carry 470 R against the Pi driving them before its I2S is up.
    """
    band_power(sh, G(27), ref_opamp=LM358)
    band_digital(sh, G(109), pi40=True)
    modulator(sh, "L", G(200), refs_for("L", 20))
    modulator(sh, "R", G(310), refs_for("R", 60))
    return sim_index(sh, G(150), G(56))


NOTE_DIGITAL_LINK = (
    "TO THE DIGITAL BOARD, 12-way IDC ribbon.  Odd pins are all GND, so\n"
    "every signal conductor has a grounded neighbour either side of it.\n"
    "Shrouded and keyed: reversed, pin 2 (+5V) would meet pin 11 (GND).")

NOTE_CHANNEL_LINK = (
    "TO CHANNEL {0}, 14-way IDC ribbon.  Both supplies, both references,\n"
    "and the three nets that carry the modulator loop across: the\n"
    "comparator out, and the DAC's two drives back to the summing\n"
    "junctions.  Odd pins are all GND.  Shrouded and keyed.")


def board_power(sh):
    """Power and the reference.  What both channels share, and nothing else.

    The quantiser and the 1-bit DAC used to live here.  That put both
    channels' loop signals on one board -- 70 % of its wire bridges were
    CMP/DAC/Q traffic -- and split each modulator loop across a cable.  They
    are on the channel board now, and this one is just the supplies.
    """
    band_power(sh, G(26), flags=("+5V", "-5V", "GND"),
               pump_x=G(62), ref_x=G(150), flag_x=G(20))
    stack_bus(sh, G(220), G(26), "J3")


def board_channel(sh, ch):
    """One modulator channel, with its ribbon back to the common board.

    Both channel boards are THE SAME ARTWORK, built twice; this is drawn once
    per channel only so that the two netlists can be checked against the
    reference sheet and against each other.  The R board's refdes are the L
    board's plus forty, and `tools/check_split.py` proves the two drawings are
    otherwise identical.
    """
    r = refs_for(ch, 20 if ch == "L" else 60)
    # Q_OUT, not QL/QR: the two channel boards are one artwork, so nothing on
    # the board may name a channel.  The shunt on J{n+1} does that, and it is
    # the only difference between the two built boards.
    modulator(sh, ch, G(31), r, qsig="Q_OUT", qnsig="QN_OUT")
    # BELOW the chain, not beside it. The modulator is one 550 mm row -- that
    # is the right drawing for a signal chain and the wrong shape to hang a
    # connector off the end of: at G(392) the header's stubs land on the
    # quantiser's own wiring and short VREF_N and -5V to the DAC drive, with
    # every geometry check still reporting the sheet as clean.
    # BELOW the chain, clear of the two TL072 supply blocks that occupy the
    # right-hand end of the modulator row -- at G(400) the socket landed on
    # the second package's decoupling cap.
    stack_bus(sh, G(200), G(140), "J7")
    q_select(sh, G(24), G(150), r["Jq"])
    power_flags(sh, G(20), G(96), ("+5V", "-5V", "GND"))


def board_digital(sh):
    """Everything clocked that is not inside the modulator loop.

    Two rows: the clock is made along the top, and the data path -- link in,
    interleave, level shift, out to the Pi -- runs along the bottom.

    Four of the nets here are drawn as WIRES rather than left to their labels,
    because on this sheet they are hops between neighbouring blocks and the
    thing a reader wants is to follow the signal with a finger.  On the
    reference sheet the very same nets cross the whole page and are correctly
    labels -- which is why each block hands back the end of its stub instead
    of deciding for itself.
    """
    y1, y2 = G(27), G(105)

    note_block(sh, (G(16), y1 - G(16)),
            "CLOCK  (6.144 MHz -> /2 BCLK 3.072M, /4 MCLK 1.536M, "
            "/32 PUMP 192k, /128 LRCLK 48k)", size=2.0)
    sel = blk_oscillator(sh, G(18), y1)
    clk6m = blk_clock_buffer(sh, G(104), y1, sel)
    div = clock_divider(sh, G(156), y1)
    blk_pi_header(sh, G(236), y1)
    # this half is powered entirely through J2, so its flags belong beside it
    power_flags(sh, G(216), y1 - G(12), ("+5V", "+3V3", "GND"))

    note_block(sh, (G(16), y2 - G(16)),
            "INTERLEAVE AND LEVEL SHIFT  (L and R onto one DIN at 3.072 Mbps, "
            "then 5 V -> 3.3 V for the Pi)", size=2.0)
    stack_bus(sh, G(24), y2, "J4")
    mux = blk_mux(sh, G(100), y2)
    lvl = blk_levelshift(sh, G(160), y2)

    elbow(sh, clk6m, (div["clk"].x - G(6), div["clk"].y), G(100))
    # MCLK, QL and QR reach the mux by global label now.  They used to be
    # drawn as wires from the ribbon header two blocks away; with the bus
    # they arrive on a connector at the far end of the sheet, and a wire
    # across that distance is less readable than the label, not more.
    # G(130) puts DIN's drop just clear of the mux's own decoupling run, which
    # falls the full height of the package from pin 16 to pin 8 beside it
    elbow(sh, mux["DIN"], lvl["DIN"], G(130))


BOARDS = {
    "vinyl_adc":           (board_full,    "A1", TITLE),
    "vinyl_adc_power":     (board_power,   "A3", TITLE + "  -  POWER BOARD"),
    "vinyl_adc_channel_l": (lambda sh: board_channel(sh, "L"), "A2",
                            TITLE + "  -  CHANNEL BOARD (built twice)"),
    "vinyl_adc_channel_r": (lambda sh: board_channel(sh, "R"), "A2",
                            TITLE + "  -  CHANNEL BOARD, R wiring"),
    "vinyl_adc_digital":   (board_digital, "A3", TITLE + "  -  DIGITAL BOARD"),
    "vinyl_adc_rev_c":     (board_rev_c,   "A1",
                            TITLE + "  -  REV C, ONE 4-LAYER BOARD"),
}


def emit_board(name, compose, paper, title):
    """Draw one sheet, check it, write it and its project.  Returns fault count."""
    sh = new_sheet(title=title, project=name, paper=paper)
    links = compose(sh) or {}

    missing = assign_footprints(sh)
    problems = sh.check()
    out = paths.sch(name)
    sh.emit(out)
    if links:
        add_hrefs(out, links)
    write_project(out, sh.uuid)

    print(f"{name}: {len(sh.parts)} symbols, "
          + ("footprints OK" if not missing else f"{len(missing)} unfootprinted")
          + ", "
          + ("geometry OK" if not problems else f"{len(problems)} geometry faults"))
    for p in problems[:20]:
        print("    ", p)
    for m in missing:
        print("     no footprint:", m)
    return len(problems) + len(missing)


def main(which="all"):
    if which == "all":
        return 1 if sum(emit_board(n, *a) for n, a in BOARDS.items()) else 0
    if which in BOARDS:
        return 1 if emit_board(which, *BOARDS[which]) else 0

    # a subset of the reference sheet's bands, for bisecting a geometry fault
    sh = new_sheet(project="bisect")
    for letter, draw in (("A", lambda: band_power(sh, G(27))),
                         ("B", lambda: band_digital(sh, G(109))),
                         ("C", lambda: modulator(sh, "L", G(191),
                                                 refs_for("L", 20))),
                         ("D", lambda: modulator(sh, "R", G(269),
                                                 refs_for("R", 60)))):
        if letter in which:
            draw()
    problems = sh.check()
    out = os.path.join(paths.ROOT, f"bisect_{which}.kicad_sch")
    sh.emit(out)
    write_project(out, sh.uuid)
    for p in problems[:40]:
        print("    ", p)
    print(f"bisect_{which}: {len(problems)} geometry faults")
    return 1 if problems else 0


if __name__ == "__main__":
    sys.exit(main(sys.argv[1] if len(sys.argv) > 1 else "all"))
