MadsRudolph/vinyl-adc/hardware/kicad/tools/make_bom.py

#!/usr/bin/env python3
"""Build the BOM and check every line against the DTU shop stock list.

Anything the shop does not carry is flagged ORDER rather than quietly listed,
because the whole design was constrained to shop parts and a silent gap there
is exactly the surprise that stops a build on the bench.

    py -3.13 make_bom.py > ../../../docs/bom.md

Reads the three ARTWORKS, not the one-page reference sheet: the artworks are
what actually gets milled, and they carry the stacking bus and the Q-select
shunt that the reference sheet has no reason to show.  Each line says which
board its parts sit on.

The channel artwork is milled TWICE -- one board is channel L, the other
channel R, and the only difference between them is which way the Q-select
shunt is fitted.  So its quantities are doubled here and its refdes are the
ones printed on the copper; the second copy carries the same ones, even though
the reference sheet numbers that channel forty higher.
"""

import collections
import csv
import os
import re
import sys
import paths

sys.path.insert(0, next(q for q in (r"C:\Users\Mads2\.claude\skills\kicad-schematic\scripts", os.path.expanduser("~/.claude/skills/kicad-schematic/scripts")) if os.path.isdir(q)))
import schlib  # noqa: E402

sys.stdout.reconfigure(encoding="utf-8")

SHOP = next(q for q in (
    r"C:\Users\Mads2\KiCad\DTU-EKB-components\Components\parts"
    r"\dtu_component_shop.csv",
    os.path.expanduser("~/Downloads/dtu_component_shop.csv"),
    os.path.expanduser("~/Downloads/Documents/dtu_component_shop.csv"),
) if os.path.exists(q))

# value -> (category hint, what to look for in the shop list)
IC_ALIASES = {"74HCT132": "74HCT132", "74HC157": "74HC157",
              "74HC4040": "74HC4040", "74HC4049": "74HC4049",
              "BC547": "BC547A"}          # the shop's grade of the same part

# rev D's LEDs carry their colour as the value; the shop lists 5 mm LEDs by
# colour in Danish
LED_SHOP = {"RED": "LED 5MM RØD", "YELLOW": "LED 5MM GUL",
            "GREEN": "LED 5MM GRØN", "WHITE": "LED 5mm Hvid"}


def load_shop():
    rows = []
    with open(SHOP, encoding="utf-8") as f:
        for r in csv.DictReader(f):
            rows.append(r)
    return rows


def norm_res(v):
    """'20k5' / '4R7' / '165k' -> ohms."""
    m = re.fullmatch(r"(\d+)([RkKMm])(\d*)", v)
    if not m:
        return None
    a, unit, b = m.groups()
    mult = {"R": 1, "k": 1e3, "K": 1e3, "M": 1e6}.get(unit, 1)
    return float(f"{a}.{b or 0}") * mult


def res_in_shop(shop, ohms):
    for r in shop:
        if r["Category"] != "Resistor" or r["Subcategory"] != "E96 Standard":
            continue
        got = norm_res(r["Part_Number"])
        if got and abs(got - ohms) < max(ohms * 0.005, 1e-9):
            return r["Part_Number"]
    return None


def cap_in_shop(shop, value):
    """value like '220p', '100n', '2u2', '470u'."""
    m = re.fullmatch(r"(\d+)([pnu])(\d*)", value)
    if not m:
        return None
    a, unit, b = m.groups()
    num = float(f"{a}.{b or 0}")
    txt = {"p": f"{num:g}pF", "n": f"{num:g}nF", "u": f"{num:g}µF"}[unit]
    for r in shop:
        if r["Category"] == "Capacitor" and r["Value"] == txt:
            return f"{r['Subcategory']} {txt}"
    return None


def ic_in_shop(shop, value):
    want = IC_ALIASES.get(value, value)
    for r in shop:
        if r["Part_Number"].upper() == want.upper():
            return f"{r['Subcategory']}"
    # the 74HC/74HCT families are listed without the HC/HCT prefix variants
    bare = re.sub(r"^74(HC|HCT|LS)", "", want)
    for r in shop:
        pn = r["Part_Number"].upper()
        if pn.endswith(bare) and pn.startswith("74"):
            return f"{r['Subcategory']} (as {r['Part_Number']})"
    return None


# tag, sheet, how many of that board a stereo ADC needs.  Three artworks,
# four boards: the channel is the one that gets milled twice.
BOARDS = (("P", "vinyl_adc_power", 1),
          ("M", "vinyl_adc_channel_l", 2),
          ("D", "vinyl_adc_digital", 1))

# `make_bom.py rev_c`: the fabricated one-board revision instead.  One
# artwork, built once, so every quantity is simply the count on the sheet.
BOARDS_REV_C = (("C", "vinyl_adc_rev_c", 1),)
# `make_bom.py rev_d`: the HAT revision, likewise one artwork built once.
BOARDS_REV_D = (("D", "vinyl_adc_rev_d", 1),)


def main():
    global BOARDS
    here = os.path.dirname(os.path.abspath(__file__))
    rev = sys.argv[1] if len(sys.argv) > 1 else ""
    rev_c = rev in ("rev_c", "rev_d")
    rev_d = rev == "rev_d"
    if rev_d:
        BOARDS = BOARDS_REV_D
    elif rev_c:
        BOARDS = BOARDS_REV_C
    shop = load_shop()

    groups = collections.defaultdict(list)
    where, mult = {}, {}
    for tag, name, n in BOARDS:
        sch = schlib.Schematic(paths.sch(name))
        for s in sch.symbols:
            ref = s.ref
            if ref.startswith("#PWR") or not ref:
                continue
            groups[(s.value, s.lib_id)].append(ref)
            where[ref] = tag
            mult[ref] = n

    def sort_key(item):
        (value, lib), refs = item
        order = {"R": 0, "C": 1, "D": 2, "U": 3, "X": 3, "J": 4, "RV": 5,
                 "FB": 2, "Y": 3}
        pfx = re.match(r"[A-Z]+", refs[0]).group()
        return (order.get(pfx, 9), value)

    lines, orders = [], []
    total = 0
    for (value, lib), refs in sorted(groups.items(), key=sort_key):
        refs = sorted(set(refs), key=lambda r: (r[0], int(re.sub(r"\D", "", r) or 0)))
        n = sum(mult[r] for r in refs)
        total += n
        pfx = re.match(r"[A-Z]+", refs[0]).group()
        avail = None
        if pfx == "R" and lib.endswith(":R"):
            ohms = norm_res(value)
            hit = res_in_shop(shop, ohms) if ohms else None
            avail = f"E96 {hit}" if hit else None
        elif pfx == "C":
            avail = cap_in_shop(shop, value)
        elif pfx in ("U", "X"):
            avail = ic_in_shop(shop, value)
        elif pfx == "RV":
            avail = "Trimmer 47K" if value == "47k" else None
        elif pfx == "D":
            avail = ic_in_shop(shop, value)
        elif pfx == "J":
            avail = {"LINE IN L": "Terminal 2 pol skrueterminal",
                     "LINE IN R": "Terminal 2 pol skrueterminal",
                     "TONEARM GND": "Terminal 2 pol skrueterminal",
                     "CLK SEL": "Header Male + Jumper",
                     "Q SEL": "Header Male + Jumper",
                     "GND LIFT": "Header Male + Jumper",
                     "WP": "Header Male + Jumper",
                     "TP L": "Header Male 2x5", "TP R": "Header Male 2x5",
                     "TP DIG": "Header Male 2x5",
                     "TO PI GPIO": "Header Male 1x8"}.get(value)
        elif pfx == "FB":
            avail = None            # axial ferrite bead: not a shop line
        elif pfx == "L":
            # the shop's low-DCR 10 uH choke; any 10 uH part rated over
            # about 0.5 A does the same job
            avail = "Inductor 10µ 3A" if value == "10u" else None
        elif pfx == "Q":
            avail = ic_in_shop(shop, value)
        elif pfx == "SW":
            avail = "Hardware Pushbutton (6 mm tactile)"
        if pfx == "D" and lib == "Device:LED":
            avail = LED_SHOP.get(value)
        status = avail or "** ORDER **"
        if not avail:
            orders.append((value, ", ".join(refs)))
        # Spell the quantity out per board rather than tagging the line with
        # the set of boards it touches. A line like 10k0 sits on power AND on
        # the channel, and only the channel half doubles -- "MP x2" reads as
        # though the whole line did, which is off by four.
        per = collections.Counter(where[r] for r in refs)
        boards = " + ".join(
            f"{tag} {per[tag]}" + (" x2" if n_boards > 1 else "")
            for tag, _name, n_boards in BOARDS if per[tag])
        lines.append((n, value, ", ".join(refs), boards, status))

    print("# Bill of materials - discrete delta-sigma vinyl ADC")
    print()
    print("Generated by `hardware/kicad/tools/make_bom.py` straight from the")
    print("schematic, with every line checked against the DTU shop stock list")
    print("(`dtu_component_shop.csv`). **ORDER** means the shop does not carry it.")
    print()
    if rev_d:
        print(f"{total} components in {len(lines)} distinct lines, for the "
              "ONE fabricated rev D board (`hardware/kicad/rev_d`): the "
              "converter as a Raspberry Pi HAT.")
        print()
        print("**Board** is always **D**: one four-layer artwork, built once, "
              "so a quantity is simply the count on the sheet. The right "
              "channel carries the reference sheet's refdes, forty higher "
              "than the left. Against rev C this adds the +5VA analog island "
              "(L2, C18, C19), a second charge-pump driver (U10), R14 in "
              "MCLK, eight status LEDs with their drivers (U12 LM339 clip "
              "detectors, Q1 clock-alive pump, Q2/Q3), two buttons, the HAT "
              "ID EEPROM (U11, optional), the chassis-ground terminal and "
              "lift network (J3, J4), and three test-point headers; L1 "
              "replaces rev C's ferrite bead with a stocked choke.")
        print()
    elif rev_c:
        print(f"{total} components in {len(lines)} distinct lines, for the "
              "ONE fabricated rev C board (`hardware/kicad/rev_c`), which "
              "replaces the four milled boards.")
        print()
        print("**Board** is always **C**: one four-layer artwork, built once, "
              "so a quantity is simply the count on the sheet. The right "
              "channel carries the reference sheet's refdes, forty higher "
              "than the left. Against the milled boards this adds U2 as an "
              "LM358 (docs/design-notes.md 10b'), FB1 on the 5 V inlet, "
              "R12/R13 in series with BCLK/LRCLK, and the Pi's own 2x20 "
              "socket J2 in place of the pigtail and stacking bus.")
        print()
    else:
        print(f"{total} components in {len(lines)} distinct lines, for the four "
              "boards a stereo ADC needs.")
        print()
        print("**Board** is **P** power (supplies and the +/-2.5 V reference), "
              "**M** modulator channel, **D** digital (clock, interleave, level "
              "shift, Pi). Three artworks, four boards: the channel is ONE "
              "artwork MILLED TWICE, so its lines are marked `M x2` and the "
              "quantity already counts both. The refdes shown are the ones "
              "printed on the copper, and the second copy carries the same ones "
              "-- the reference sheet numbers that channel forty higher, the "
              "board does not.")
        print()
    print("| Qty | Value | Refs | Board | DTU shop |")
    print("|----:|-------|------|-------|----------|")
    for n, value, refs, boards, status in lines:
        print(f"| {n} | {value} | {refs} | {boards} | {status} |")
    print()
    if orders:
        print("## Must be ordered")
        print()
        for v, refs in orders:
            print(f"- **{v}** ({refs})")
    else:
        print("Everything on this list is stocked by the shop.")
    print()
    print("## Sockets")
    print()
    print("Use DIP sockets for every IC (all stocked): 8-pin for the TL072s")
    print("and the LM311s, 14-pin for the 74HC04 / 74HCU04 / 74HC74 /")
    print("74HCT132, 16-pin for the 74HC157 / 74HC4040 / 74HC4049, 20-pin for")
    print("the 74HC244. The crystal Y1 solders in directly.")
    if rev_d:
        print()
        print("Also 8-pin for the LM358 and the 24LC32, 14-pin for the LM339. "
              "J2 is a 2x20 FEMALE header on the copper side (a plain 8.5 mm "
              "HAT socket; an 11 mm extended-height one if the Pi's PoE header "
              "touches the leads at the socket's top end). L1 and L2 are the "
              "shop's 10 uH 3 A choke on a 15.24 mm axial footprint. The LEDs "
              "are 5 mm, colours as in the Value column; the buttons are 6 mm "
              "tactile. Four M2.5 standoffs (11 mm) carry the Pi under the "
              "board, four M3 the board in its enclosure.")
    elif rev_c:
        print()
        print("J2 is a 2x20 FEMALE header on the copper side (a plain 8.5 mm "
              "HAT socket; an 11 mm extended-height one if the Pi's PoE header "
              "touches the leads at the socket's top end). FB1 is any axial "
              "ferrite bead on a lead, 10.16 mm pitch -- or a wire link. The "
              "board also wants four M2.5 standoffs for the Pi and four M3 for "
              "the enclosure.")
    print()
    if rev_c:
        return
    print("## The stacking bus")
    print()
    print("There are no ribbons. Every board carries the SAME 2x8 on 2.54 mm")
    print("at the SAME coordinates, and the four boards plug into each other")
    print("on 11 mm standoffs:")
    print()
    print("| Board | Ref | Ways | Position in the stack |")
    print("|---|---|---|---|")
    print("| digital | J4 | 2x8 | top |")
    print("| channel L | J7 | 2x8 | middle |")
    print("| channel R | J7 | 2x8 | middle |")
    print("| power | J3 | 2x8 | bottom |")
    print()
    print("Odd pins are all GND, so every signal has a grounded neighbour")
    print("either side -- which is what MCLK needs, its jitter being what sets")
    print("this converter's noise floor. The even pins carry, in order:")
    print("**+5V, VREF_P, VREF_N, MCLK, PUMP, QL, QR, -5V**.")
    print()
    print("What goes in the sixteen holes is a build choice, not an artwork")
    print("choice: a plain socket on the top board, a long-pin header on the")
    print("bottom one, and a pass-through stacking header on the two in the")
    print("middle. All three are the same sixteen pads. You need 4 sets plus")
    print("16 x 11 mm M3 standoffs and the M3 screws; the shop carries none of")
    print("them, so they go on the same order as the 74HCU04.")
    print()
    print("## Which channel is which")
    print()
    print("Both channel boards are the same copper, so nothing etched on them")
    print("says which channel a board is. The Q-select shunt does: **J21 1-2")
    print("makes it LEFT, 2-3 makes it RIGHT**. Fit one jumper per channel")
    print("board and they are otherwise interchangeable.")


if __name__ == "__main__":
    main()
