MadsRudolph/vinyl-adc/hardware/kicad/sim/tools/run_sims.py

#!/usr/bin/env python
r"""Export each testbench through KiCad, run it, and check the DESIGN's numbers.

    C:\Users\Mads2\miniconda3\python.exe tools\run_sims.py [a b c ...]

Verification harness only.  The sheets themselves are ordinary KiCad
schematics that run in Eeschema's own simulator; this exports the same
netlist KiCad would hand ngspice and asserts what docs/design-notes.md says
the circuit does, so a broken testbench is caught here rather than by eye.

Every bound below comes from the design record, not from what the models
happen to do -- tools/test_models.py is where the models answer to their
datasheets.  A model and a check that shared an assumption would agree with
each other and both be wrong, which is exactly how an inverted comparator
model once passed its own test on another board.
"""
import subprocess
import sys
import time
from pathlib import Path

import numpy as np
from PySpice.Spice.NgSpice.Shared import NgSpiceShared

KICAD_CLI = next(p for p in (r"C:\Program Files\KiCad\10.0\bin\kicad-cli.exe",
                             "/usr/bin/kicad-cli") if Path(p).exists())
SIM = Path(__file__).resolve().parent.parent
NG = NgSpiceShared.new_instance(verbose=False)
RESULTS = []

# from docs/design-notes.md section 3, the state scales in volts per unit
S1, S2, S3 = 2.04, 1.79, 1.47
V_D = 2.5                      # DAC half-swing
F_MCLK = 1.536e6


# ----------------------------------------------------------------- plumbing
def netlist(bench):
    out = SIM / "build" / f"{bench}.cir"
    out.parent.mkdir(exist_ok=True)
    r = subprocess.run([KICAD_CLI, "sch", "export", "netlist", "--format",
                        "spice", "-o", str(out),
                        str(SIM / f"{bench}.kicad_sch")],
                       capture_output=True, text=True)
    if r.returncode:
        raise SystemExit(f"{bench}: netlist export failed\n{r.stdout}{r.stderr}")
    return out.read_text(encoding="utf-8")


def simulate(deck):
    try:
        NG.remove_circuit()
    except Exception:  # noqa: BLE001 - nothing loaded on the first call
        pass
    NG.load_circuit(deck)
    try:
        NG.run()
    except Exception:  # noqa: BLE001
        # ngspice returns a non-zero status whenever it fell back on dynamic
        # gmin stepping, which it does for any deck whose operating point
        # starts with an amplifier against its clamp -- and then runs the
        # analysis perfectly.  The plot is the real test.
        pass
    plot = NG.plot(None, NG.last_plot)
    w = {k.lower(): np.asarray(v.to_waveform()) for k, v in plot.items()}
    if len(w.get("time", ())) < 2:
        raise RuntimeError("analysis produced no data")
    return w


def check(name, got, lo, hi, unit=""):
    ok = got is not None and np.isfinite(got) and lo <= got <= hi
    RESULTS.append((ok, name))
    g = "None" if got is None else f"{got:.5g}"
    print(f"    {'PASS' if ok else 'FAIL'}  {name:50s} {g:>11}{unit}"
          f"  want {lo:g}..{hi:g}{unit}")


def report(name, value, unit=""):
    """A measurement worth printing that is not a pass/fail claim."""
    print(f"    ....  {name:50s} {value:>11.5g}{unit}")


def edges(t, v, level=2.5, rising=True):
    out = []
    for i in range(1, len(v)):
        a, b = v[i - 1], v[i]
        if (rising and a < level <= b) or (not rising and a > level >= b):
            f = (level - a) / (b - a) if b != a else 0.0
            out.append(t[i - 1] + f * (t[i] - t[i - 1]))
    return np.array(out)


def freq(t, v, level=2.5):
    e = edges(t, v, level)
    return 1.0 / np.mean(np.diff(e)) if len(e) > 2 else None


def duty(t, v, level=2.5):
    up, dn = edges(t, v, level, True), edges(t, v, level, False)
    if len(up) < 3 or len(dn) < 3:
        return None
    period = float(np.mean(np.diff(up)))
    dn = dn[dn > up[0]]
    n = min(len(up), len(dn))
    return float(np.mean(dn[:n] - up[:n])) / period * 100.0


def detrended_pp(t, v):
    """Peak-to-peak with any linear drift removed."""
    res = v - np.polyval(np.polyfit(t, v, 1), t)
    return float(res.max() - res.min())


def window(t, lo, hi):
    return (t >= lo) & (t <= hi)


def ramp_rates(t, v, drive, hold, t0, t1, frac=(0.55, 0.95)):
    """Settled integrator ramp rate between DAC edges, in V/s, up and down.

    A 3 MHz op-amp takes about three time constants -- 150 ns -- to reach
    full slope after each DAC edge, so the MEDIAN instantaneous slope over a
    651 ns half period reads 4 % low and the triangle's peak-to-peak reads
    6 % low.  Neither is a loss of charge: the amplifier delivers all of it,
    just late.  So fit the settled part of each ramp, and report the rounding
    separately rather than letting it masquerade as a wrong coefficient.
    """
    ups = [e for e in edges(t, drive) if t0 < e < t1]
    dns = [e for e in edges(t, drive, rising=False) if t0 < e < t1]
    out = []
    for group in (ups, dns):
        slopes = []
        for e in group:
            sel = window(t, e + frac[0] * hold, e + frac[1] * hold)
            if sel.sum() > 3:
                slopes.append(np.polyfit(t[sel], v[sel], 1)[0])
        out.append(float(np.median(slopes)) if slopes else float("nan"))
    return out[0], out[1]


# ------------------------------------------------------------------ benches
def bench_a():
    """The charge pump: -5 V rail, ripple, and that it inverts at all."""
    w = simulate(netlist("sim_a_pump"))
    t, v, node = w["time"], w["-5v"], w["pumpnode"]

    # THE polarity check.  Both Schottkys were drawn backwards, which makes
    # this a voltage doubler putting +3.4 V on every op-amp's V- pin; every
    # other gate in the toolkit passed that version, because a diode wired
    # the wrong way round is still a connected diode.
    check("pump node swings below the negative rail (V)",
          float(node.min()), -5.0, -3.0, " V")
    check("pump node never rises far above ground (V)",
          float(node.max()), -0.1, 1.0, " V")

    final = float(v[-1])
    report("settled rail", final, " V")
    report("load current", abs(final) / 130.0 * 1e3, " mA")
    # the design's requirement, not its estimate: the TL074s must clear a
    # 1.94 V peak swing, and the part needs about 1.5 V of headroom
    check("rail deep enough for a 1.94 V peak swing (V)", final, -4.6, -3.44,
          " V")
    # docs/design-notes.md 6: ripple below 1 uV after 4R75 + 220u
    T = 32.0 / 6.144e6
    sel = t > t[-1] - 2 * T
    check("ripple after the RC filter (uV)",
          detrended_pp(t[sel], v[sel]) * 1e6, 0, 1.0, " uV")
    # and it has to be up before the analog section is asked to work
    half = float(v[np.searchsorted(t, 40e-3)])
    check("rail within 5 % of final by 40 ms (V)", half, final * 1.05,
          final * 0.95, " V")


def bench_b():
    """The reference: 2.5 V, and ratiometric to the rail moment by moment."""
    w = simulate(netlist("sim_b_reference"))
    t = w["time"]
    sel = t > 0.2e-3
    p, n, rail = w["vref_p"][sel], w["vref_n"][sel], w["+5v"][sel]
    check("VREF_P mean (V)", float(p.mean()), 2.495, 2.505, " V")
    check("VREF_N mean (V)", float(n.mean()), -2.505, -2.495, " V")
    # the point of the whole block: rail noise must arrive as a common-mode
    # gain modulation, which is only true if VREF tracks the rail exactly
    check("worst |VREF_P - rail/2| (uV)",
          float(np.max(np.abs(p - rail / 2))) * 1e6, 0, 1000, " uV")
    check("worst |VREF_N + VREF_P| (uV)",
          float(np.max(np.abs(n + p))) * 1e6, 0, 1000, " uV")
    # 100 mV of hum on a 5 V rail is a 2 % modulation; -98 dB of it survives
    ripple = float(p.max() - p.min())
    report("VREF_P follows the rail's 100 mV hum by", ripple * 1e3, " mVpp")


def bench_c():
    """The divider: four exact binary clocks, and how much skew they cost."""
    w = simulate(netlist("sim_c_clock"))
    t = w["time"]
    sel = t > 5e-6
    tt = t[sel]
    for node, want in (("bclk", 3.072e6), ("mclk", 1.536e6),
                       ("pump", 192e3), ("lrclk", 48e3)):
        f = freq(tt, w[node][sel])
        check(f"{node.upper()} frequency (kHz)", f / 1e3 if f else None,
              want * 0.995 / 1e3, want * 1.005 / 1e3, " kHz")
    for node in ("bclk", "mclk", "pump"):
        check(f"{node.upper()} duty (%)", duty(tt, w[node][sel]), 49, 51, " %")
    check("BCLK swings the rail (Vpp)",
          float(w["bclk"][sel].max() - w["bclk"][sel].min()), 4.9, 5.05, " Vpp")
    # the HCT buffer's whole job: a 3.3 V source still clocks a 5 V chain
    check("a 3.3 V source still drives CLK6M to the rail (Vpp)",
          float(w["clk6m"][sel].max() - w["clk6m"][sel].min()), 4.9, 5.05,
          " Vpp")
    # ripple skew: every extra stage delays its output, and that comes
    # straight off the 163 ns of I2S setup margin (docs/design-notes.md 4b)
    eb = edges(tt, w["bclk"][sel], rising=False)
    el = edges(tt, w["lrclk"][sel], rising=False)
    skew = min(abs(x - eb[np.argmin(np.abs(eb - x))]) for x in el[1:4])
    report("BCLK to LRCLK ripple skew", skew * 1e9, " ns")
    check("ripple skew leaves the setup margin intact (ns)", skew * 1e9,
          0, 100, " ns")
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
